PingvinOpenTag/LTAscetic/release_2(LCD,Joystck,TouchMemory,Reload,Antichiter,IrPowerControl,BattaryControl)/hardware/pcb/FreePCB/lib_extra/sm_ipc782.pdf

c:\freepcb_1000\lib_extra\sm_ipc782.pdf | page 1

## I2012CHIP

Author: Ivex
Source: SURFACE MOUNT DESIGN AND LAND PATTERN STANDARD SUBSECTION 8.3 (PAGE 3 OF 4)
Size: 3.6 x 1.6 mm
PIN(s) | PAD
TYPE | SHAPE | SIZE | HOLE
1-2 | SMT | Square | 1 mm | ---

Scale 2:1

## I3216CHIP

Author: Ivex
Source: SURFACE MOUNT DESIGN AND LAND PATTERN STANDARD SUBSECTION 8.3 (PAGE 3 OF 4)
Size: 4.9 x 2.2 mm
PIN(s) | PAD
TYPE | SHAPE | SIZE | HOLE
1-2 | SMT | Rect | 1.3 x 1.6 mm | ---

Scale 2:1

## I4516CHIP

Author: Ivex
Source: SURFACE MOUNT DESIGN AND LAND PATTERN STANDARD SUBSECTION 8.3 (PAGE 3 OF 4)
Size: 6.4 x 1.6 mm
PIN(s) | PAD
TYPE | SHAPE | SIZE | HOLE
1-2 | SMT | Rect | 1.6 x 1 mm | ---

Scale 2:1

## I2825PREC

Author: Ivex
Source: SURFACE MOUNT DESIGN AND LAND PATTERN STANDARD SUBSECTION 8.3 (PAGE 3 OF 4)
Size: 4.4 x 3 mm
PIN(s) | PAD
TYPE | SHAPE | SIZE | HOLE
1-2 | SMT | Rect | 1.4 x 2.4 mm | ---

Scale 2:1

## I3225PREC

Author: Ivex
Source: SURFACE MOUNT DESIGN AND LAND PATTERN STANDARD SUBSECTION 8.3 (PAGE 3 OF 4)
Size: 5.2 x 2.6 mm
PIN(s) | PAD
TYPE | SHAPE | SIZE | HOLE
1-2 | SMT | Rect | 1.8 x 2 mm | ---

## I4532PREC

Author: Ivex
Source: SURFACE MOUNT DESIGN AND LAND PATTERN STANDARD SUBSECTION 8.3 (PAGE 3 OF 4)
Size: 6.4 x 4.2 mm
PIN(s) | PAD
TYPE | SHAPE | SIZE | HOLE
1-2 | SMT | Rect | 1.8 x 3.6 mm | ---

Scale 2:1

## I5038PREC

Author: Ivex
Source: SURFACE MOUNT DESIGN AND LAND PATTERN STANDARD SUBSECTION 8.3 (PAGE 3 OF 4)
Size: 6.4 x 3.4 mm
PIN(s) | PAD
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
PIN(s) | PAD
TYPE | SHAPE | SIZE | HOLE
1-36 | SMT | Rect | 0.65 x 2.2 mm | ---

Scale 1:1

## CFP-MO-023/50

Author: Ivex
Source: - IPC-SM-782, REVISION A - AUGUST 1993 Size: 32.76 x 28.2 mm
PIN(s) | PAD
TYPE | SHAPE | SIZE | HOLE
1-50 | SMT | Rect | 0.65 x 2.2 mm | ---

Scale 1:1
