PingvinOpenTag/LTAscetic/release_1/hardware/pcb/layout.pdf

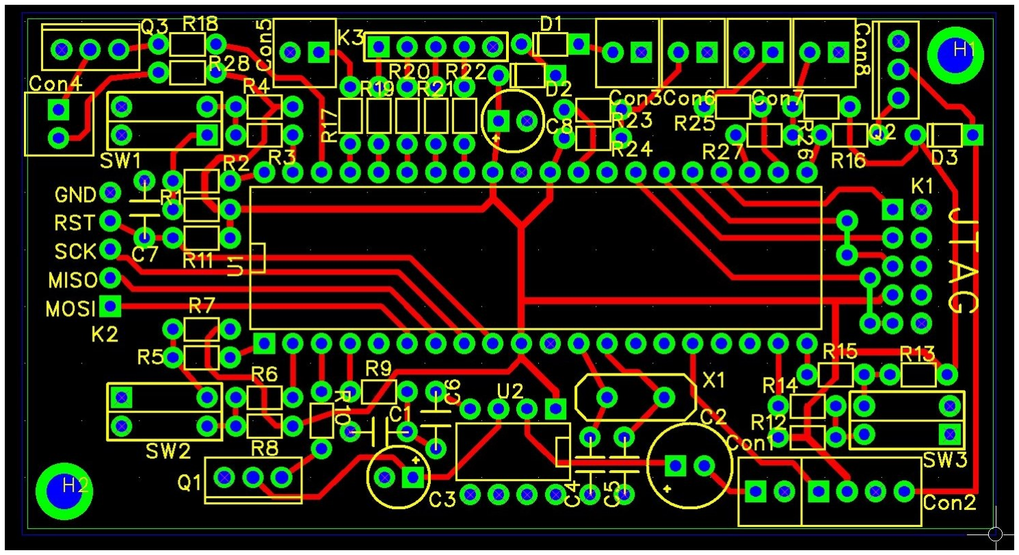
[picture p4: figure]
