PingvinOpenTag/LTAscetic/5_provodov.jpg

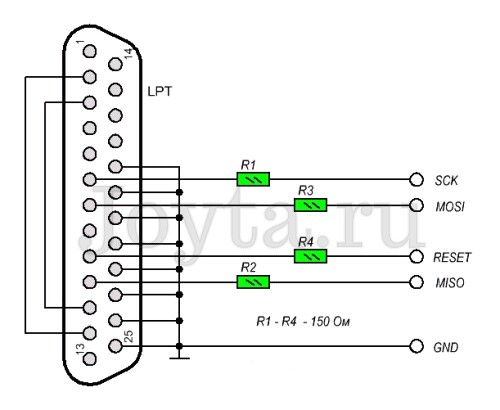
5_provodov.jpg
