PingvinOpenTag/LTAscetic/programmer.gif

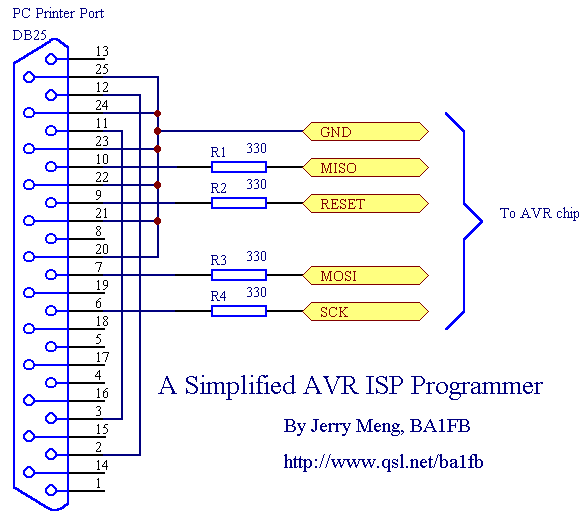
programmer.gif
