PingvinOpenTag/LTAscetic/release_2(LCD,Joystck,TouchMemory,Reload,Antichiter,IrPowerControl,BattaryControl)/hardware/scheme/lcd_shield_smd_scheme.jpeg

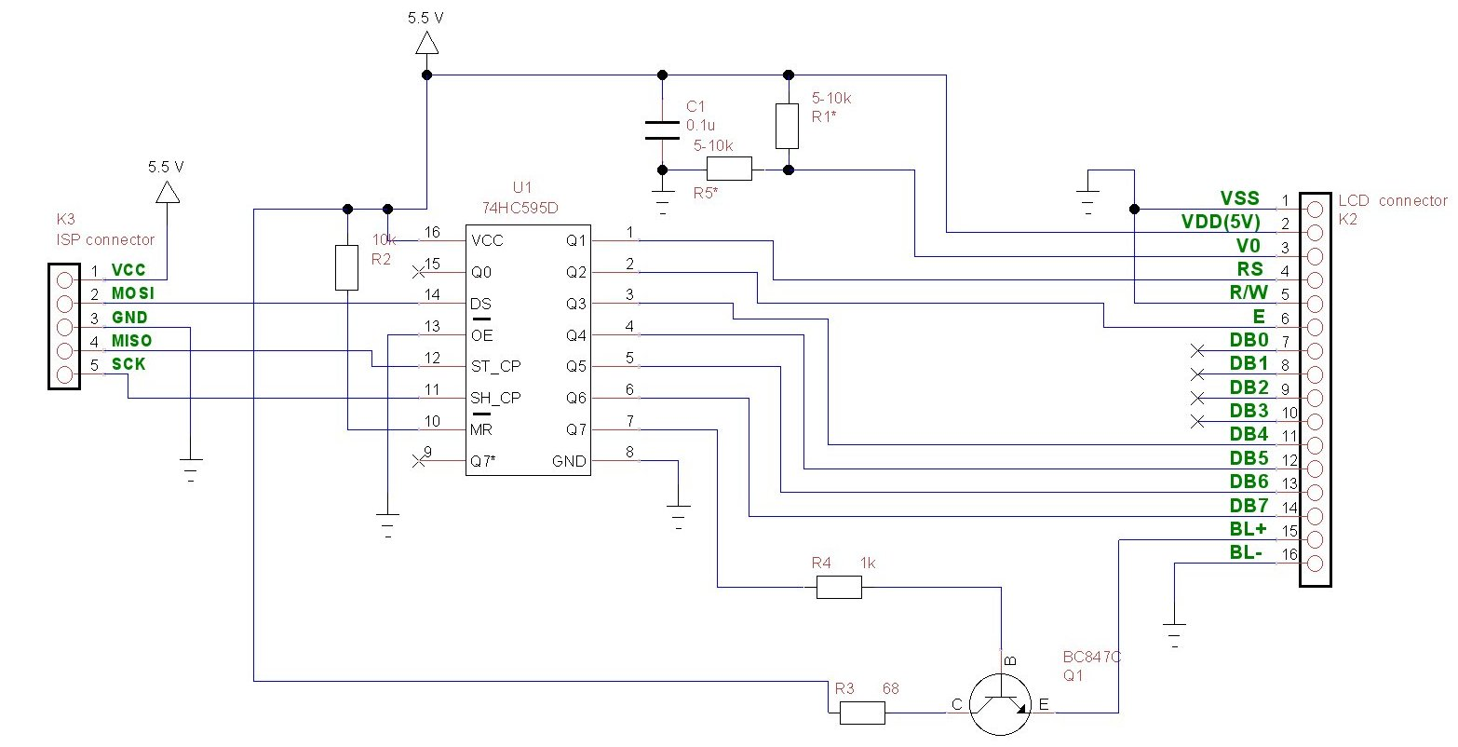
release_2(LCD,Joystck,TouchMemory,Reload,Antichiter,IrPowerControl,BattaryControl)/hardware/scheme/lcd_shield_smd_scheme.jpeg
