PingvinOpenTag/LTAscetic/release_3(all_thet_is_in_the_release_2,extern_EEPROM_RS232_BOOTLOADER)/firmware/LTAscetic_Atmega32/Ascet_3_0_with_bootloader_fuses_AVRStudio4.png

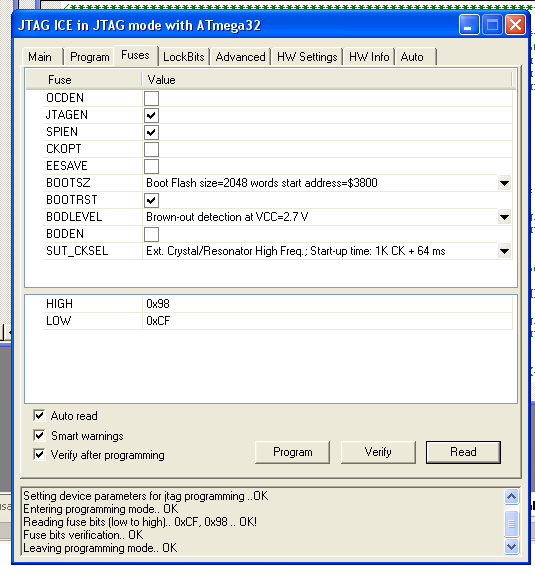
release_3(all_thet_is_in_the_release_2,extern_EEPROM_RS232_BOOTLOADER)/firmware/LTAscetic_Atmega32/Ascet_3_0_with_bootloader_fuses_AVRStudio4.png
