PingvinOpenTag/LTAscetic/release_3(all_thet_is_in_the_release_2,extern_EEPROM_RS232_BOOTLOADER)/hardware/scheme/Ascetic_3_LCD_shield_scheme.jpeg

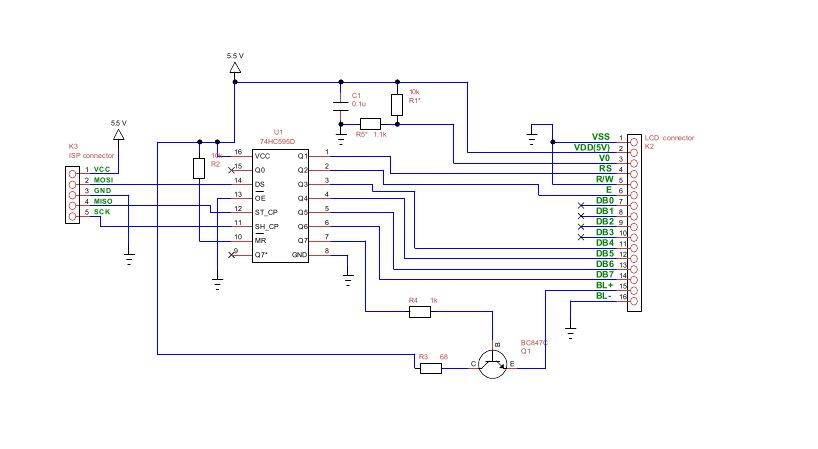
release_3(all_thet_is_in_the_release_2,extern_EEPROM_RS232_BOOTLOADER)/hardware/scheme/Ascetic_3_LCD_shield_scheme.jpeg
