PingvinOpenTag/LTAscetic/release_3_1(SMD,fix_flesh_led_bag,firmware_up_to_56000Hz_IR_F0)/hardware/scheme/Ascet_3_1_IR_Sensor_scheme.jpeg

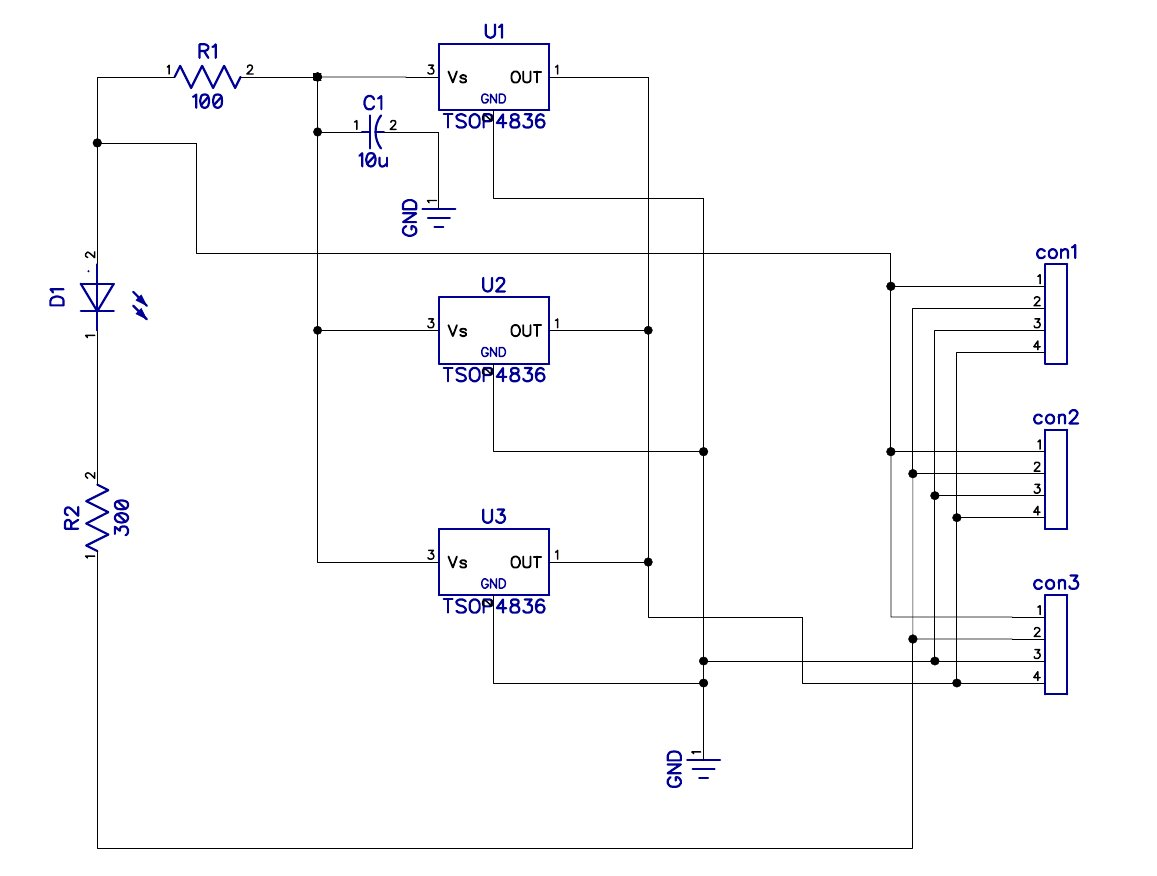
release_3_1(SMD,fix_flesh_led_bag,firmware_up_to_56000Hz_IR_F0)/hardware/scheme/Ascet_3_1_IR_Sensor_scheme.jpeg
