PingvinOpenTag/LTAscetic/release_3_1(SMD,fix_flesh_led_bag,firmware_up_to_56000Hz_IR_F0)/firmware/LTAscet_3_1_Atmega32/Ascet_3_1_without_bootloader_PonyProg_fuses.jpeg

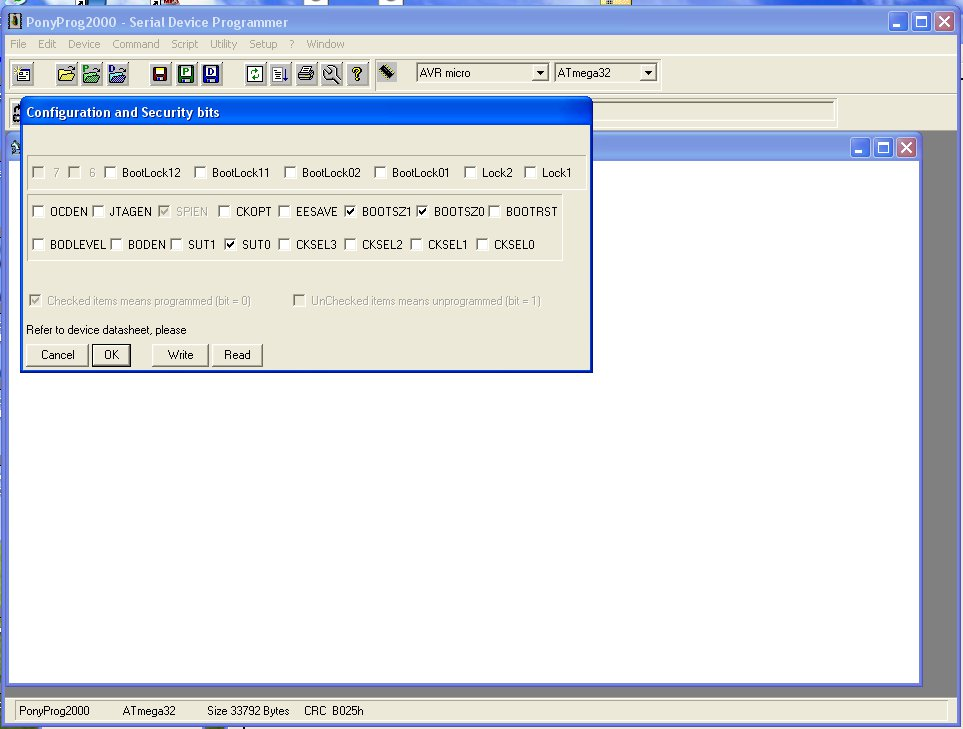
release_3_1(SMD,fix_flesh_led_bag,firmware_up_to_56000Hz_IR_F0)/firmware/LTAscet_3_1_Atmega32/Ascet_3_1_without_bootloader_PonyProg_fuses.jpeg
