PingvinOpenTag/LTAscetic/release_2(LCD,Joystck,TouchMemory,Reload,Antichiter,IrPowerControl,BattaryControl)/hardware/pcb/FreePCB/lib_extra/elfa_cap.pdf

1206

0805

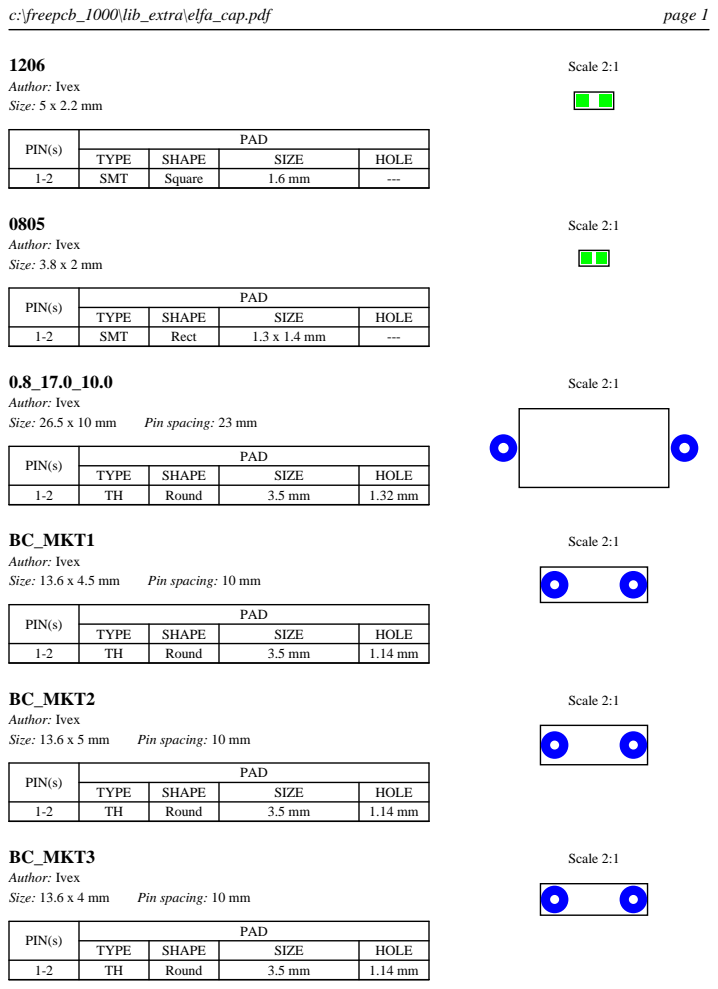
[picture p30: page 1]
c:\freepcb_1000\lib_extra\elfa_cap.pdf; page 1; Author: Ivex Size: 5 x 2.2 mm; Scale 2:1; Author: Ivex Size: 3.8 x 2 mm; Author: Ivex; Size: 26.5 x 10 mm; Pin spacing: 23 mm; BC_MKT1; Size: 13.6 x 4.5 mm; Pin spacing: 10 mm; BC_MKT2; Size: 13.6 x 5 mm; BC_MKT3; Size: 13.6 x 4 mm

PIN(s) | PAD

TYPE | SHAPE | SIZE | HOLE

1-2 | SMT | Square | 1.6 mm | ---

1-2 | SMT | Rect | 1.3 x 1.4 mm | ---

1-2 | TH | Round | 3.5 mm | 1.32 mm

1-2 | TH | Round | 3.5 mm | 1.14 mm

## BC_MKT4

## BC_MKT5

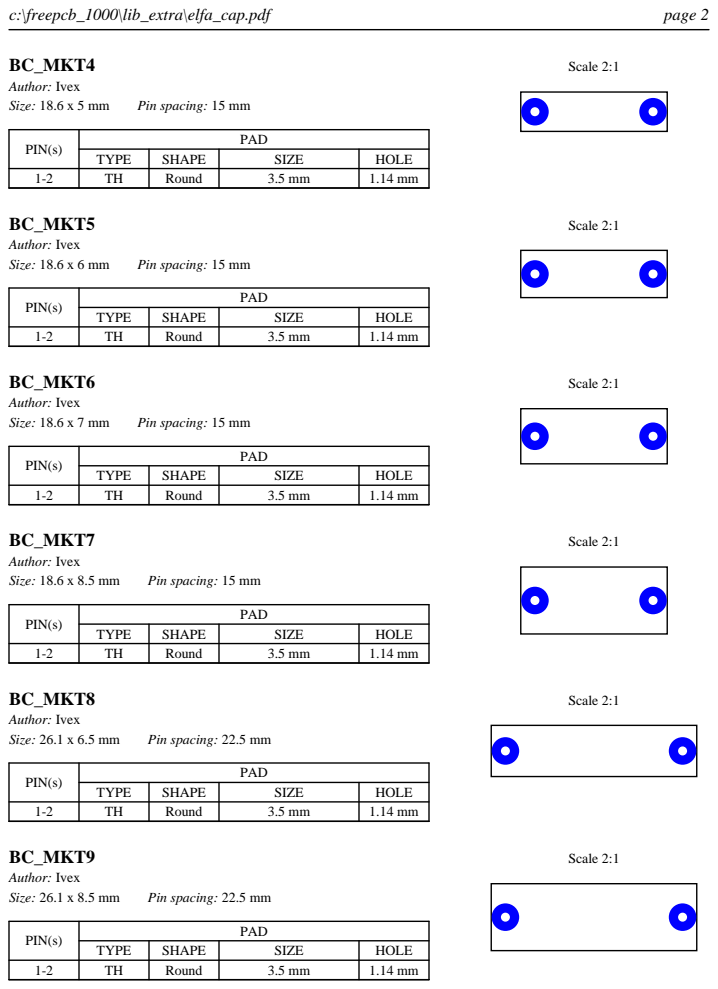
[picture p31: page 2]
Author: Ivex; Size: 18.6 x 5 mm; Pin spacing: 15 mm; Size: 18.6 x 6 mm; Scale 2:1; BC_MKT6; Size: 18.6 x 7 mm; BC_MKT7; Size: 18.6 x 8.5 mm; BC_MKT8; Size: 26.1 x 6.5 mm; Pin spacing: 22.5 mm; BC_MKT9; Size: 26.1 x 8.5 mm

PIN(s) | PAD

TYPE | SHAPE | SIZE | HOLE

1-2 | TH | Round | 3.5 mm | 1.14 mm

## BC_MKT10

## BC_MKT11

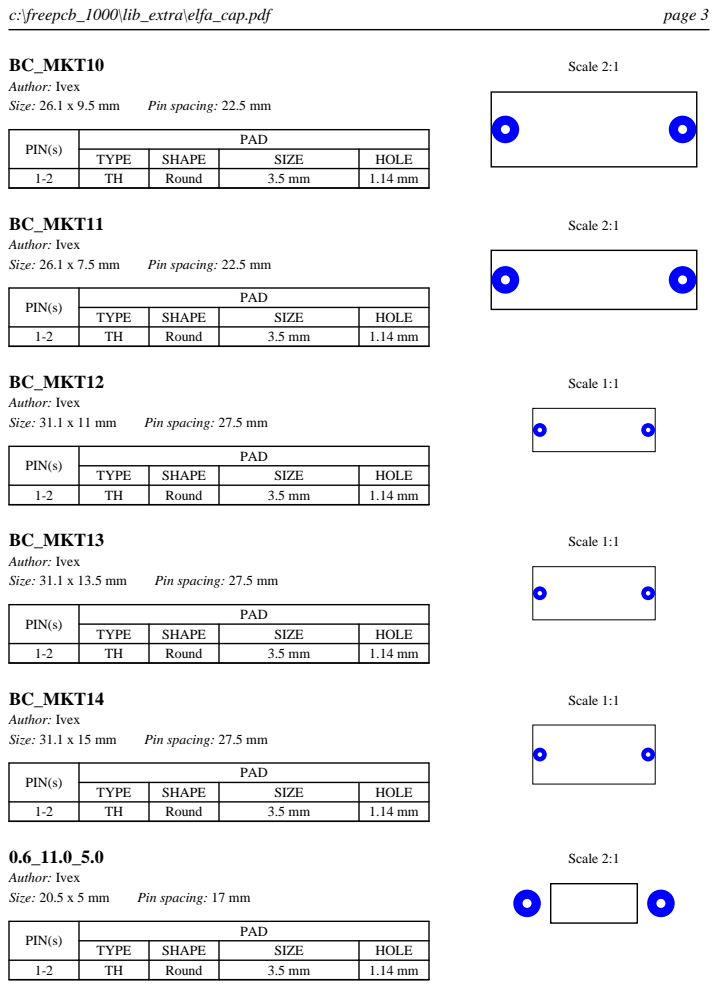
[picture p32: page 3]
Author: Ivex; Size: 26.1 x 9.5 mm; Pin spacing: 22.5 mm; Size: 26.1 x 7.5 mm; Scale 2:1; BC_MKT12; Size: 31.1 x 11 mm; Pin spacing: 27.5 mm; Scale 1:1; BC_MKT13; Size: 31.1 x 13.5 mm; BC_MKT14; Size: 31.1 x 15 mm; Size: 20.5 x 5 mm; Pin spacing: 17 mm

PIN(s) | PAD

TYPE | SHAPE | SIZE | HOLE

1-2 | TH | Round | 3.5 mm | 1.14 mm

0.6_15.0_5.5

0.6_15.0_6.0

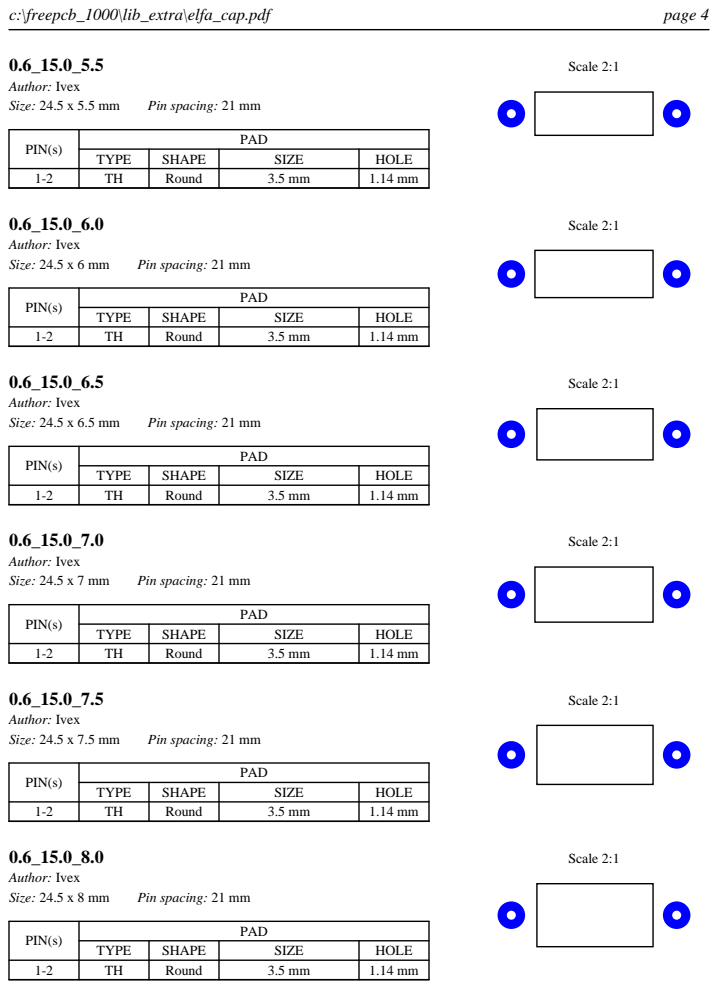
[picture p33: page 4]
Author: Ivex; Size: 24.5 x 5.5 mm; Pin spacing: 21 mm; Size: 24.5 x 6 mm; Scale 2:1; Size: 24.5 x 6.5 mm; Size: 24.5 x 7 mm; Size: 24.5 x 7.5 mm; Size: 24.5 x 8 mm

PIN(s) | PAD

TYPE | SHAPE | SIZE | HOLE

1-2 | TH | Round | 3.5 mm | 1.14 mm

## BC_LS2.54

## BC_LS5.08

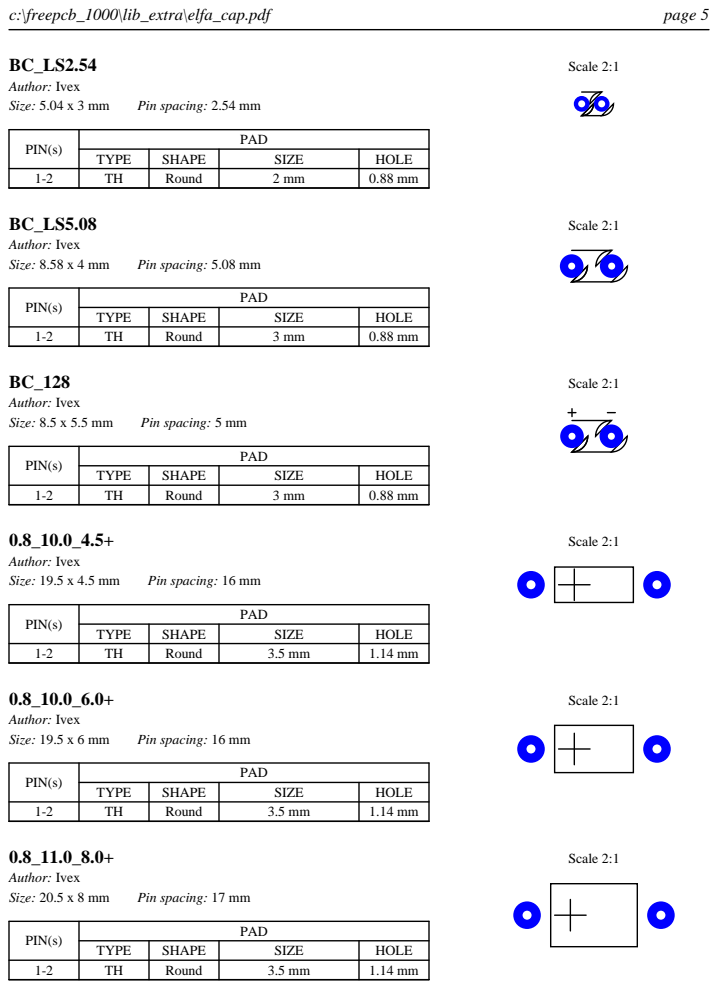
[picture p34: page 5]
Author: Ivex; Size: 5.04 x 3 mm; Pin spacing: 2.54 mm; Size: 8.58 x 4 mm; Pin spacing: 5.08 mm; Scale 2:1; Size: 8.5 x 5.5 mm; Pin spacing: 5 mm; Size: 19.5 x 4.5 mm; Pin spacing: 16 mm; Size: 19.5 x 6 mm; Size: 20.5 x 8 mm; Pin spacing: 17 mm

PIN(s) | PAD

TYPE | SHAPE | SIZE | HOLE

1-2 | TH | Round | 2 mm | 0.88 mm

1-2 | TH | Round | 3 mm | 0.88 mm

1-2 | TH | Round | 3.5 mm | 1.14 mm

0.8_18.0_10.0+

0.8_18.0_8.0+

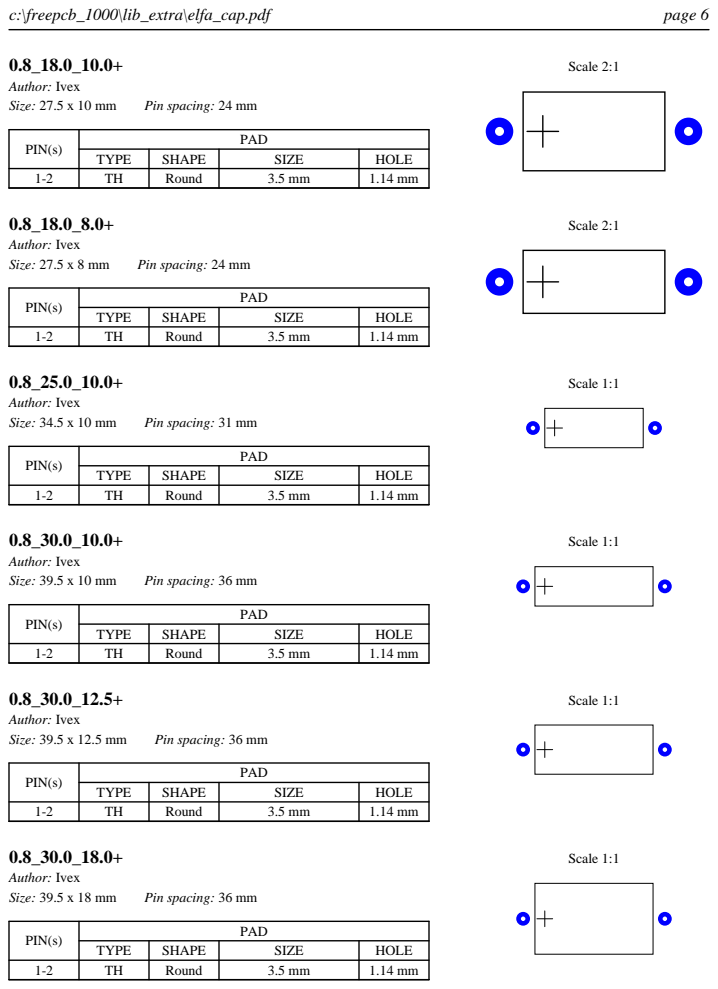
[picture p35: page 6]
Author: Ivex; Size: 27.5 x 10 mm; Pin spacing: 24 mm; Size: 27.5 x 8 mm; Scale 2:1; Size: 34.5 x 10 mm; Pin spacing: 31 mm; Scale 1:1; Size: 39.5 x 10 mm; Pin spacing: 36 mm; Size: 39.5 x 12.5 mm; Size: 39.5 x 18 mm

PIN(s) | PAD

TYPE | SHAPE | SIZE | HOLE

1-2 | TH | Round | 3.5 mm | 1.14 mm

0.8_40.0_21.0+

0.8_36.0_14.0+

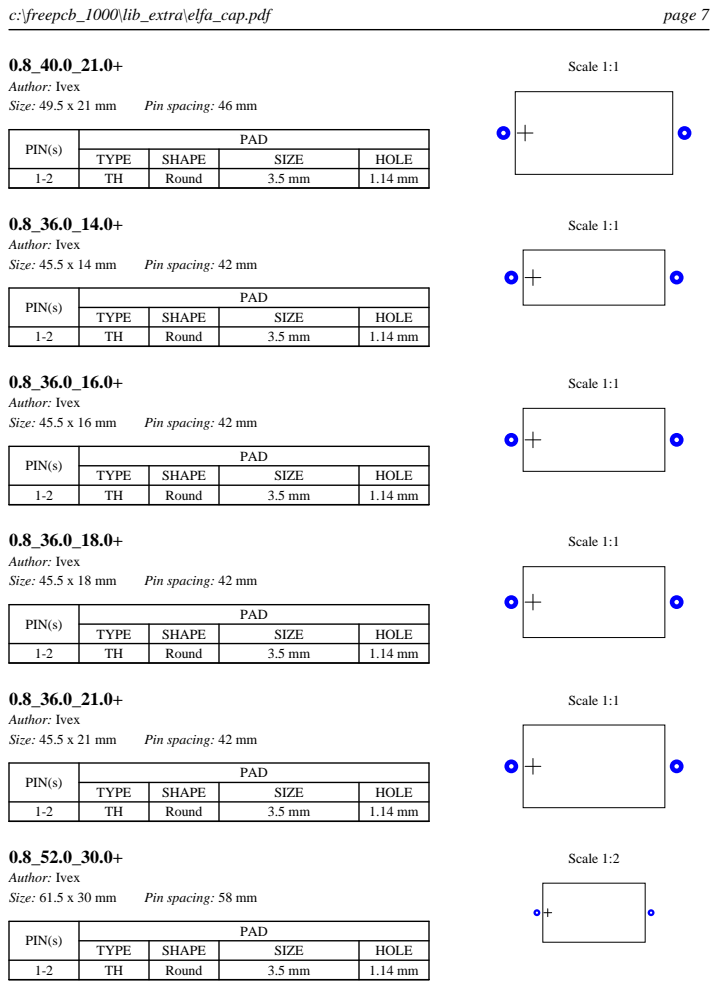
[picture p36: page 7]
Author: Ivex; Size: 49.5 x 21 mm; Pin spacing: 46 mm; Scale 1:1; Size: 45.5 x 14 mm; Pin spacing: 42 mm; Size: 45.5 x 16 mm; Size: 45.5 x 18 mm; Size: 45.5 x 21 mm; Size: 61.5 x 30 mm; Pin spacing: 58 mm; Scale 1:2

PIN(s) | PAD

TYPE | SHAPE | SIZE | HOLE

1-2 | TH | Round | 3.5 mm | 1.14 mm

0.8_49.0_25.0+

0.8_18.0_6.5+

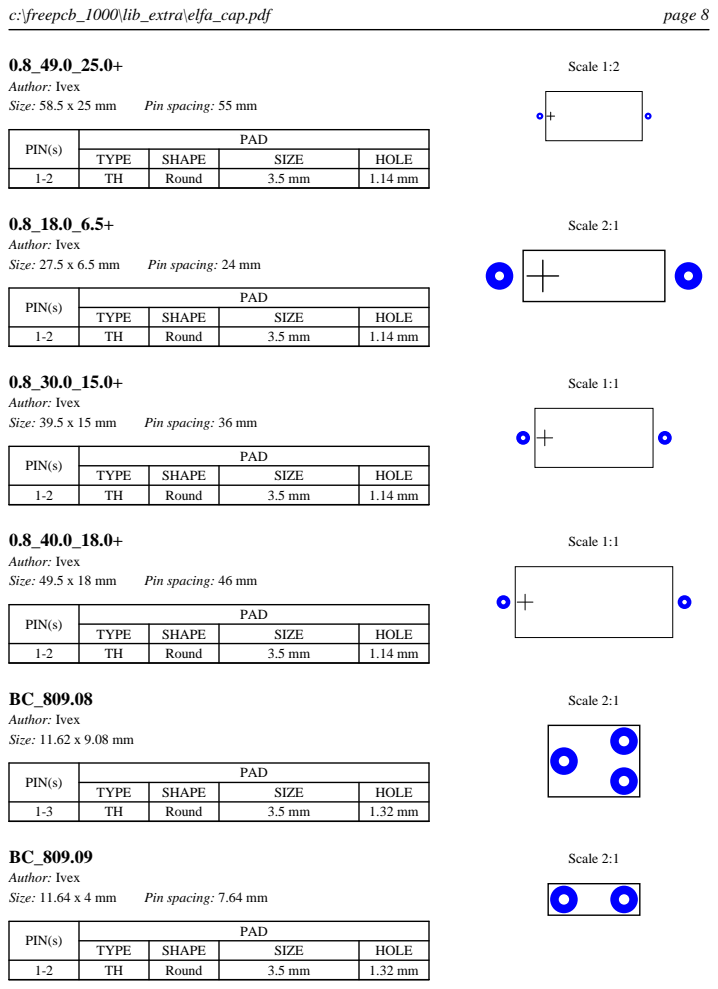
[picture p37: page 8]
Author: Ivex; Size: 58.5 x 25 mm; Pin spacing: 55 mm; Scale 1:2; Size: 27.5 x 6.5 mm; Pin spacing: 24 mm; Scale 2:1; Size: 39.5 x 15 mm; Pin spacing: 36 mm; Scale 1:1; Size: 49.5 x 18 mm; Pin spacing: 46 mm; Author: Ivex Size: 11.62 x 9.08 mm; Size: 11.64 x 4 mm; Pin spacing: 7.64 mm

PIN(s) | PAD

TYPE | SHAPE | SIZE | HOLE

1-2 | TH | Round | 3.5 mm | 1.14 mm

1-3 | TH | Round | 3.5 mm | 1.32 mm

1-2 | TH | Round | 3.5 mm | 1.32 mm

## BC_808.11

## ELNA_RJH8

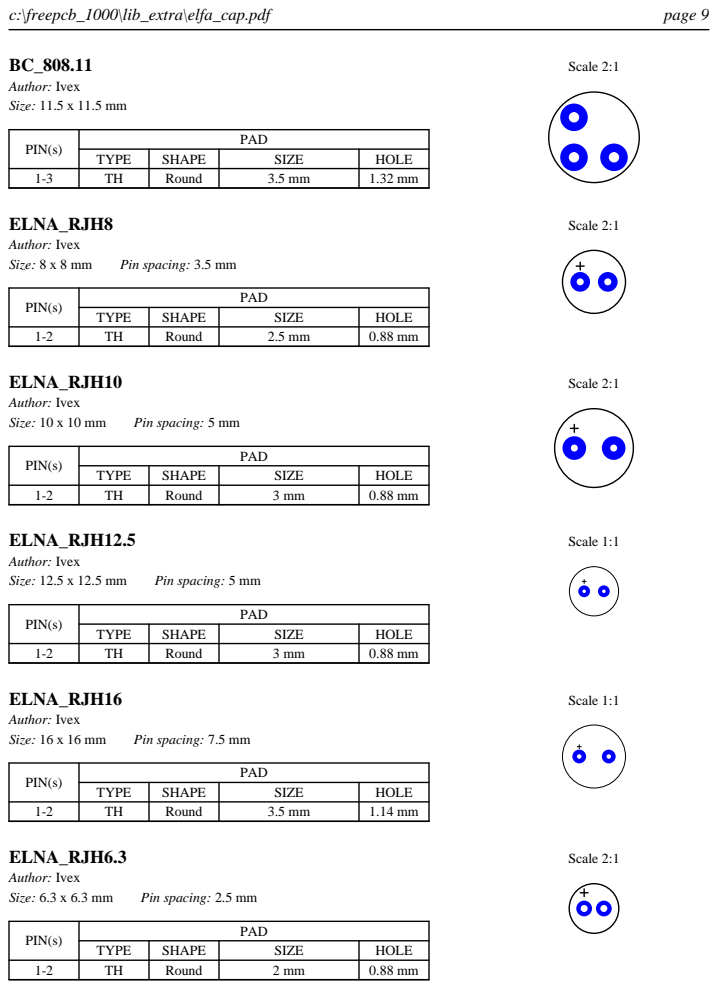
[picture p38: page 9]
Author: Ivex Size: 11.5 x 11.5 mm; Author: Ivex; Size: 8 x 8 mm; Pin spacing: 3.5 mm; Scale 2:1; ELNA_RJH10; Size: 10 x 10 mm; Pin spacing: 5 mm; ELNA_RJH12.5; Size: 12.5 x 12.5 mm; Scale 1:1; ELNA_RJH16; Size: 16 x 16 mm; Pin spacing: 7.5 mm; ELNA_RJH6.3; Size: 6.3 x 6.3 mm; Pin spacing: 2.5 mm

PIN(s) | PAD

TYPE | SHAPE | SIZE | HOLE

1-3 | TH | Round | 3.5 mm | 1.32 mm

1-2 | TH | Round | 2.5 mm | 0.88 mm

1-2 | TH | Round | 3 mm | 0.88 mm

1-2 | TH | Round | 3.5 mm | 1.14 mm

1-2 | TH | Round | 2 mm | 0.88 mm

## ELNA_RJH5

## ELNA_RJH18

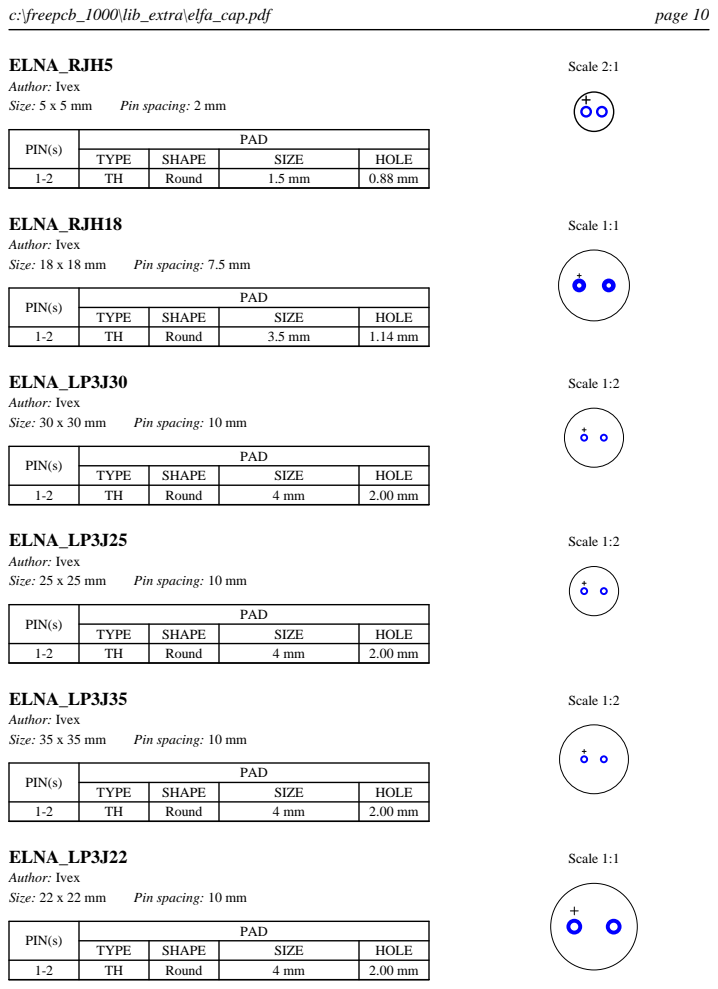
[picture p39: page 10]
Author: Ivex; Size: 5 x 5 mm; Pin spacing: 2 mm; Size: 18 x 18 mm; Pin spacing: 7.5 mm; Scale 1:1; ELNA_LP3J30; Size: 30 x 30 mm; Pin spacing: 10 mm; Scale 1:2; ELNA_LP3J25; Size: 25 x 25 mm; ELNA_LP3J35; Size: 35 x 35 mm; ELNA_LP3J22; Size: 22 x 22 mm

PIN(s) | PAD

TYPE | SHAPE | SIZE | HOLE

1-2 | TH | Round | 1.5 mm | 0.88 mm

1-2 | TH | Round | 3.5 mm | 1.14 mm

1-2 | TH | Round | 4 mm | 2.00 mm

## ELNA_DB13.5

## ELNA_DB21.5

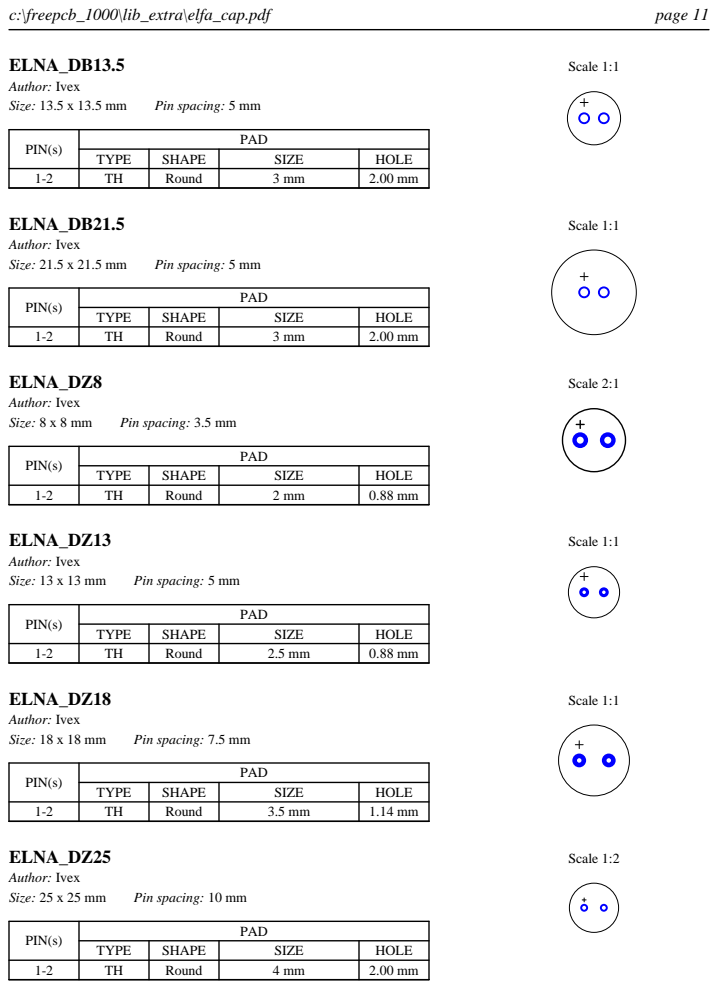
[picture p40: page 11]
Author: Ivex; Size: 13.5 x 13.5 mm; Pin spacing: 5 mm; Scale 1:1; Size: 21.5 x 21.5 mm; ELNA_DZ8; Size: 8 x 8 mm; Pin spacing: 3.5 mm; Scale 2:1; ELNA_DZ13; Size: 13 x 13 mm; ELNA_DZ18; Size: 18 x 18 mm; Pin spacing: 7.5 mm; ELNA_DZ25; Size: 25 x 25 mm; Pin spacing: 10 mm; Scale 1:2

PIN(s) | PAD

TYPE | SHAPE | SIZE | HOLE

1-2 | TH | Round | 3 mm | 2.00 mm

1-2 | TH | Round | 2 mm | 0.88 mm

1-2 | TH | Round | 2.5 mm | 0.88 mm

1-2 | TH | Round | 3.5 mm | 1.14 mm

1-2 | TH | Round | 4 mm | 2.00 mm

## JAM_4

## JAM_5

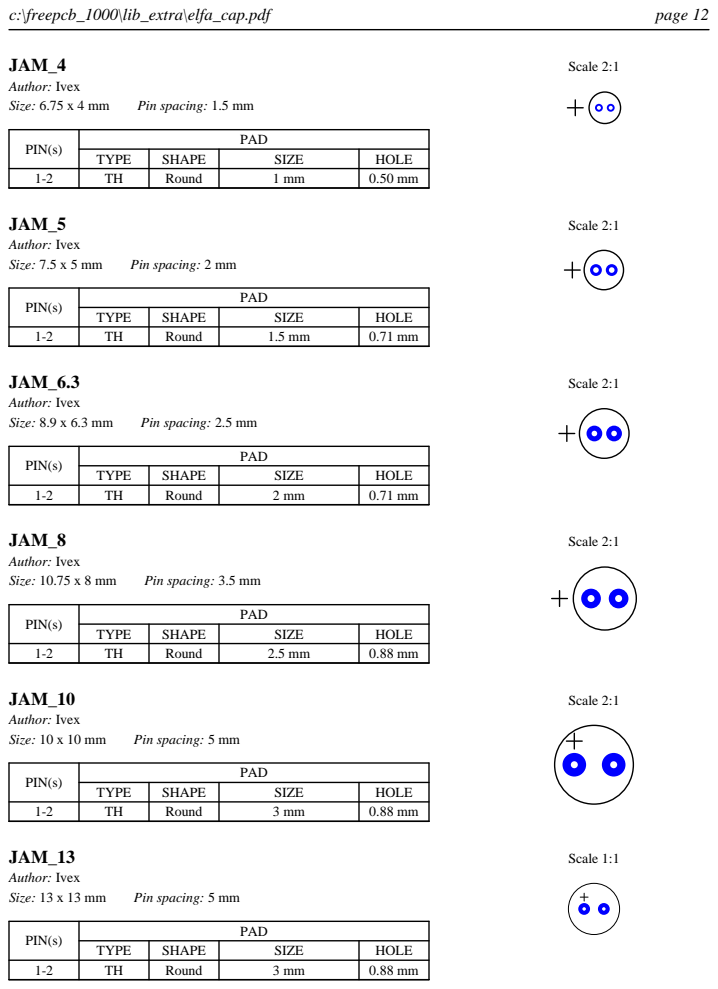
[picture p41: page 12]
Author: Ivex; Size: 6.75 x 4 mm; Pin spacing: 1.5 mm; Size: 7.5 x 5 mm; Pin spacing: 2 mm; Scale 2:1; JAM_6.3; Size: 8.9 x 6.3 mm; Pin spacing: 2.5 mm; JAM_8; Size: 10.75 x 8 mm; Pin spacing: 3.5 mm; JAM_10; Size: 10 x 10 mm; Pin spacing: 5 mm; JAM_13; Size: 13 x 13 mm; Scale 1:1

PIN(s) | PAD

TYPE | SHAPE | SIZE | HOLE

1-2 | TH | Round | 1 mm | 0.50 mm

1-2 | TH | Round | 1.5 mm | 0.71 mm

1-2 | TH | Round | 2 mm | 0.71 mm

1-2 | TH | Round | 2.5 mm | 0.88 mm

1-2 | TH | Round | 3 mm | 0.88 mm

## JAM_16

## JAM_18

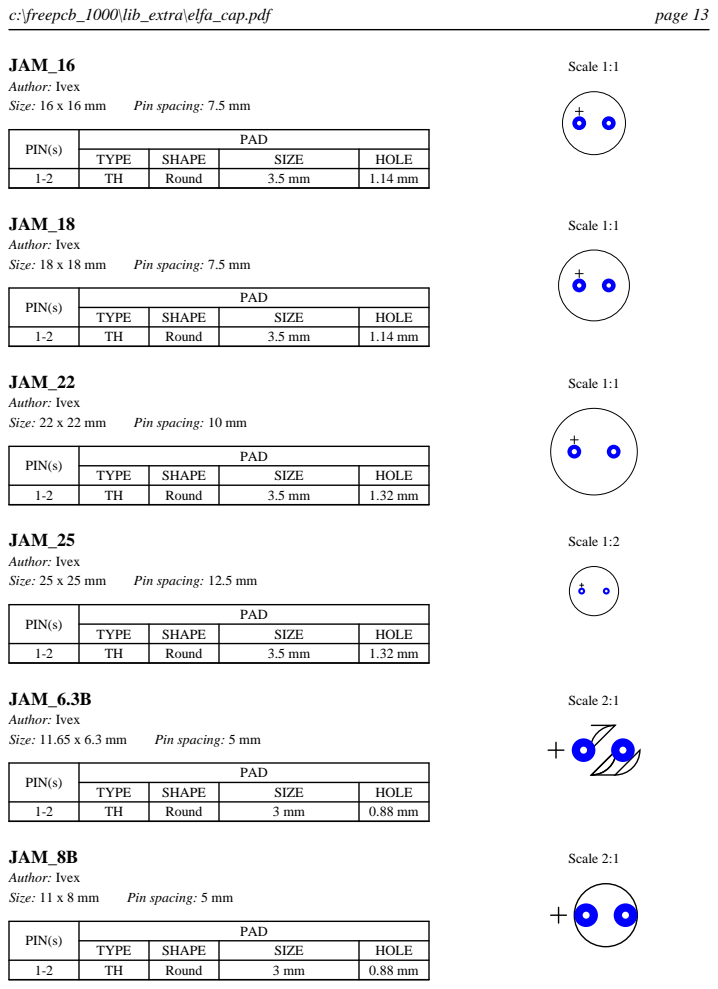
[picture p42: page 13]
Author: Ivex; Size: 16 x 16 mm; Pin spacing: 7.5 mm; Scale 1:1; Size: 18 x 18 mm; JAM_22; Size: 22 x 22 mm; Pin spacing: 10 mm; JAM_25; Size: 25 x 25 mm; Pin spacing: 12.5 mm; Scale 1:2; JAM_6.3B; Size: 11.65 x 6.3 mm; Pin spacing: 5 mm; Scale 2:1; JAM_8B; Size: 11 x 8 mm

PIN(s) | PAD

TYPE | SHAPE | SIZE | HOLE

1-2 | TH | Round | 3.5 mm | 1.14 mm

1-2 | TH | Round | 3.5 mm | 1.32 mm

1-2 | TH | Round | 3 mm | 0.88 mm

## JAM_5B

## KEM_C315/C320

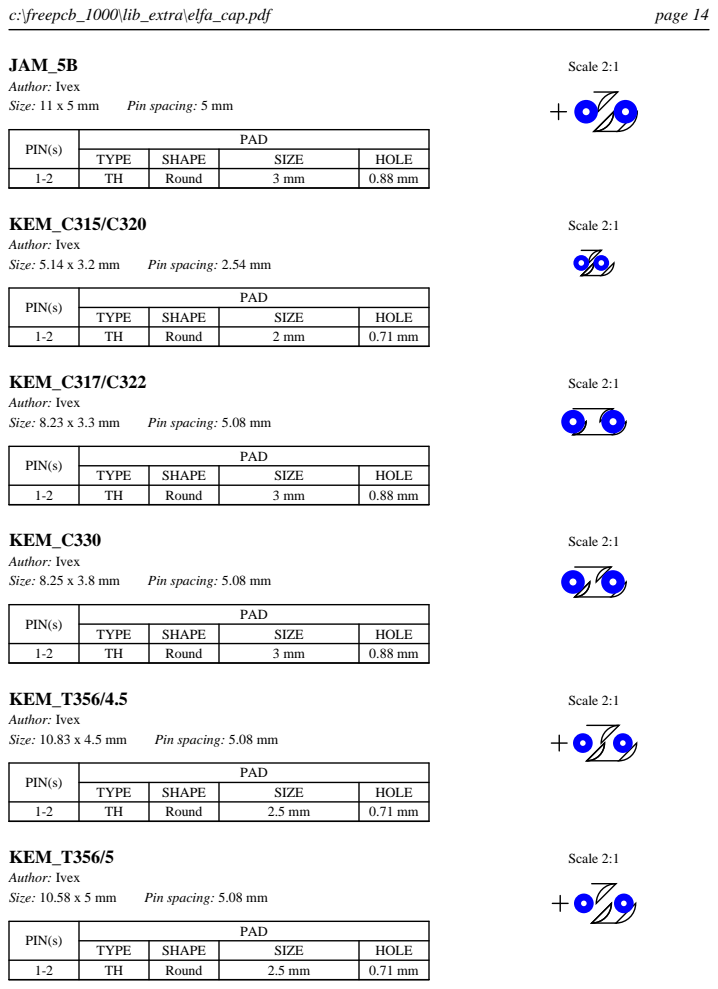
[picture p43: page 14]
Author: Ivex; Size: 11 x 5 mm; Pin spacing: 5 mm; Size: 5.14 x 3.2 mm; Pin spacing: 2.54 mm; Scale 2:1; KEM_C317/C322; Size: 8.23 x 3.3 mm; Pin spacing: 5.08 mm; KEM_C330; Size: 8.25 x 3.8 mm; KEM_T356/4.5; Size: 10.83 x 4.5 mm; KEM_T356/5; Size: 10.58 x 5 mm

PIN(s) | PAD

TYPE | SHAPE | SIZE | HOLE

1-2 | TH | Round | 3 mm | 0.88 mm

1-2 | TH | Round | 2 mm | 0.71 mm

1-2 | TH | Round | 2.5 mm | 0.71 mm

## KEM_T356/5.5

## KEM_T356/6

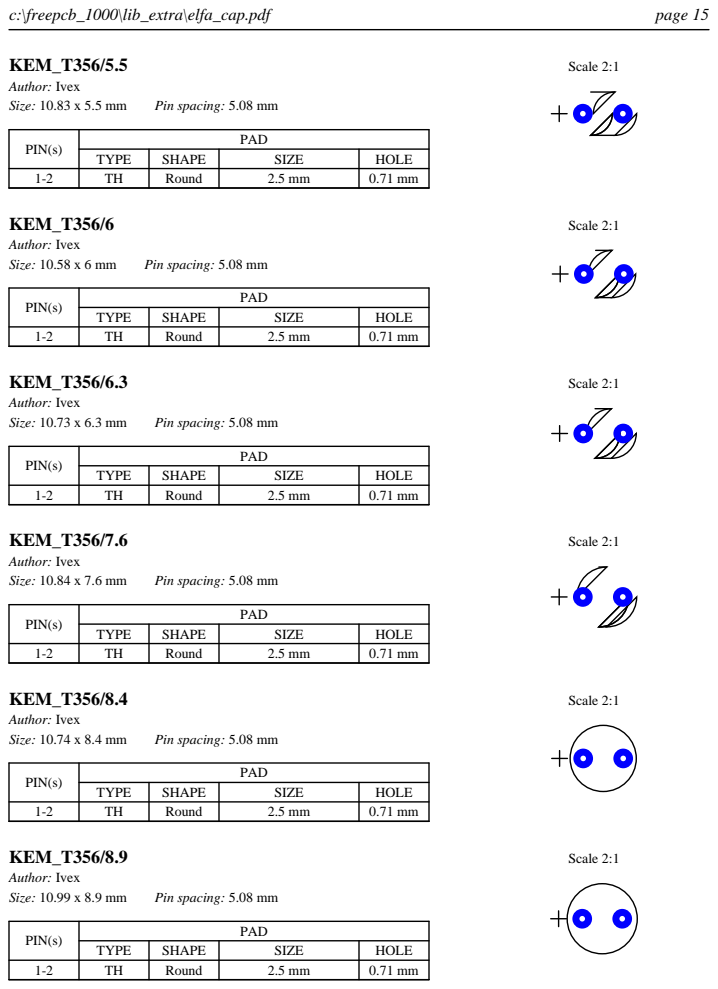
[picture p44: page 15]
Author: Ivex; Size: 10.83 x 5.5 mm; Pin spacing: 5.08 mm; Size: 10.58 x 6 mm; Scale 2:1; KEM_T356/6.3; Size: 10.73 x 6.3 mm; KEM_T356/7.6; Size: 10.84 x 7.6 mm; KEM_T356/8.4; Size: 10.74 x 8.4 mm; KEM_T356/8.9; Size: 10.99 x 8.9 mm

PIN(s) | PAD

TYPE | SHAPE | SIZE | HOLE

1-2 | TH | Round | 2.5 mm | 0.71 mm

## KEM_T350/4.5

## KEM_T350/5.0

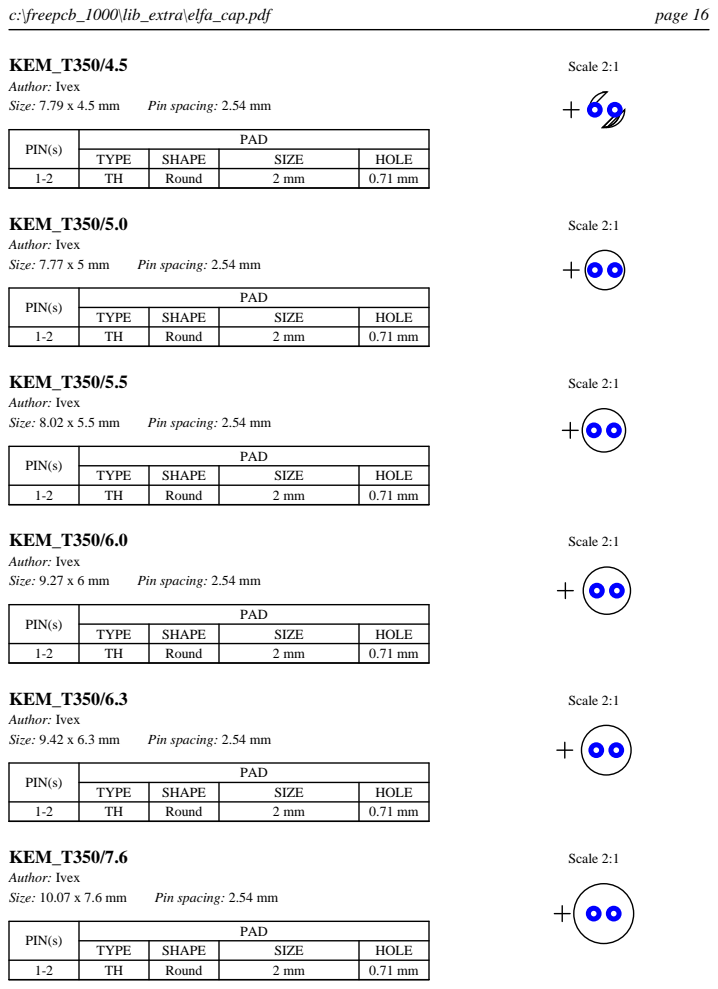
[picture p45: page 16]
Author: Ivex; Size: 7.79 x 4.5 mm; Pin spacing: 2.54 mm; Size: 7.77 x 5 mm; Scale 2:1; KEM_T350/5.5; Size: 8.02 x 5.5 mm; KEM_T350/6.0; Size: 9.27 x 6 mm; KEM_T350/6.3; Size: 9.42 x 6.3 mm; KEM_T350/7.6; Size: 10.07 x 7.6 mm

PIN(s) | PAD

TYPE | SHAPE | SIZE | HOLE

1-2 | TH | Round | 2 mm | 0.71 mm

## KEM_AXL12.7

## KEM_AXL17.8

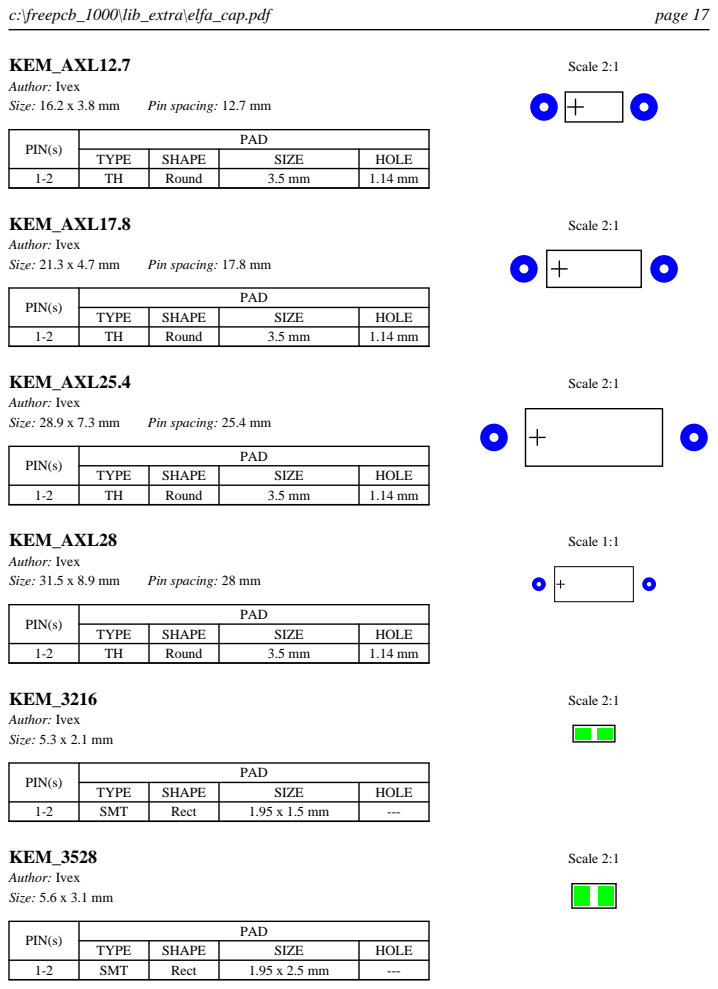
[picture p46: page 17]
Author: Ivex; Size: 16.2 x 3.8 mm; Pin spacing: 12.7 mm; Size: 21.3 x 4.7 mm; Pin spacing: 17.8 mm; Scale 2:1; KEM_AXL25.4; Size: 28.9 x 7.3 mm; Pin spacing: 25.4 mm; KEM_AXL28; Size: 31.5 x 8.9 mm; Pin spacing: 28 mm; Scale 1:1; KEM_3216; Author: Ivex Size: 5.3 x 2.1 mm; KEM_3528; Author: Ivex Size: 5.6 x 3.1 mm

PIN(s) | PAD

TYPE | SHAPE | SIZE | HOLE

1-2 | TH | Round | 3.5 mm | 1.14 mm

1-2 | SMT | Rect | 1.95 x 1.5 mm | ---

1-2 | SMT | Rect | 1.95 x 2.5 mm | ---

## KEM_6032

## KEM_7343

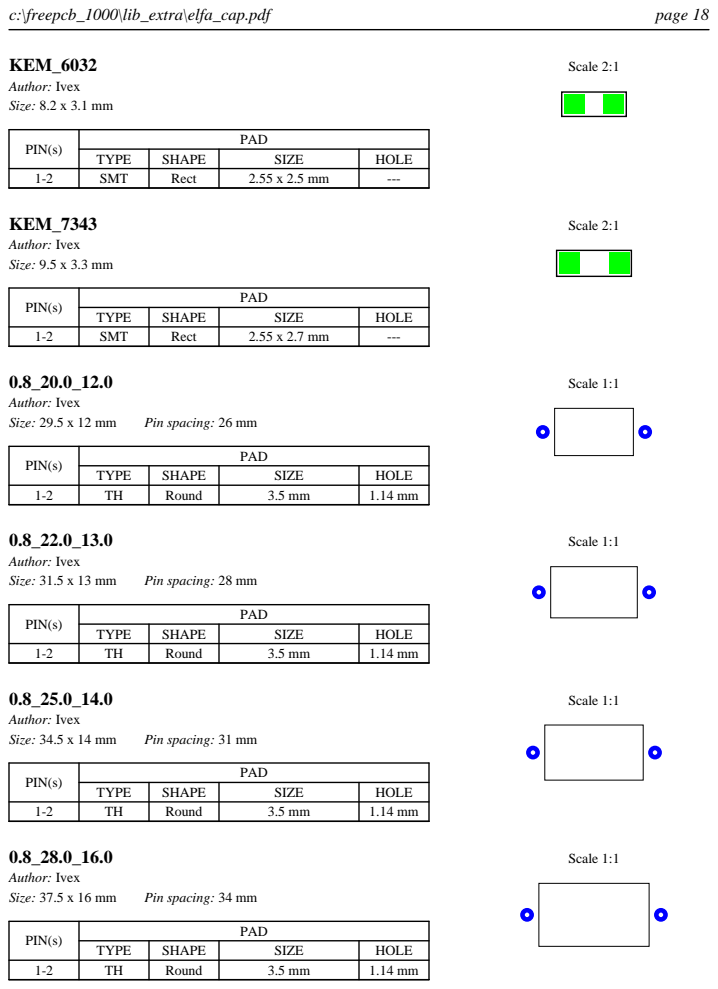
[picture p47: page 18]
Author: Ivex Size: 8.2 x 3.1 mm; Author: Ivex Size: 9.5 x 3.3 mm; Scale 2:1; Author: Ivex; Size: 29.5 x 12 mm; Pin spacing: 26 mm; Scale 1:1; Size: 31.5 x 13 mm; Pin spacing: 28 mm; Size: 34.5 x 14 mm; Pin spacing: 31 mm; Size: 37.5 x 16 mm; Pin spacing: 34 mm

PIN(s) | PAD

TYPE | SHAPE | SIZE | HOLE

1-2 | SMT | Rect | 2.55 x 2.5 mm | ---

1-2 | SMT | Rect | 2.55 x 2.7 mm | ---

1-2 | TH | Round | 3.5 mm | 1.14 mm

0.8_28.0_19.0

0.8_30.0_19.0

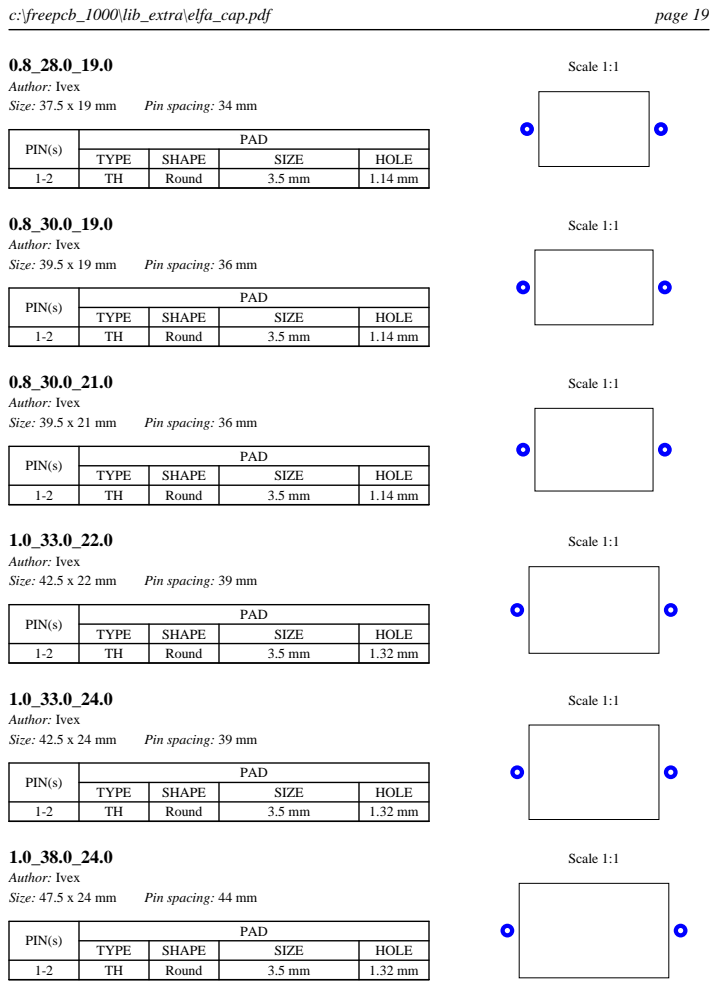
[picture p48: page 19]
Author: Ivex; Size: 37.5 x 19 mm; Pin spacing: 34 mm; Scale 1:1; Size: 39.5 x 19 mm; Pin spacing: 36 mm; Size: 39.5 x 21 mm; Size: 42.5 x 22 mm; Pin spacing: 39 mm; Size: 42.5 x 24 mm; Size: 47.5 x 24 mm; Pin spacing: 44 mm

PIN(s) | PAD

TYPE | SHAPE | SIZE | HOLE

1-2 | TH | Round | 3.5 mm | 1.14 mm

1-2 | TH | Round | 3.5 mm | 1.32 mm

1.0_38.0_26.0

1.0_43.0_26.0

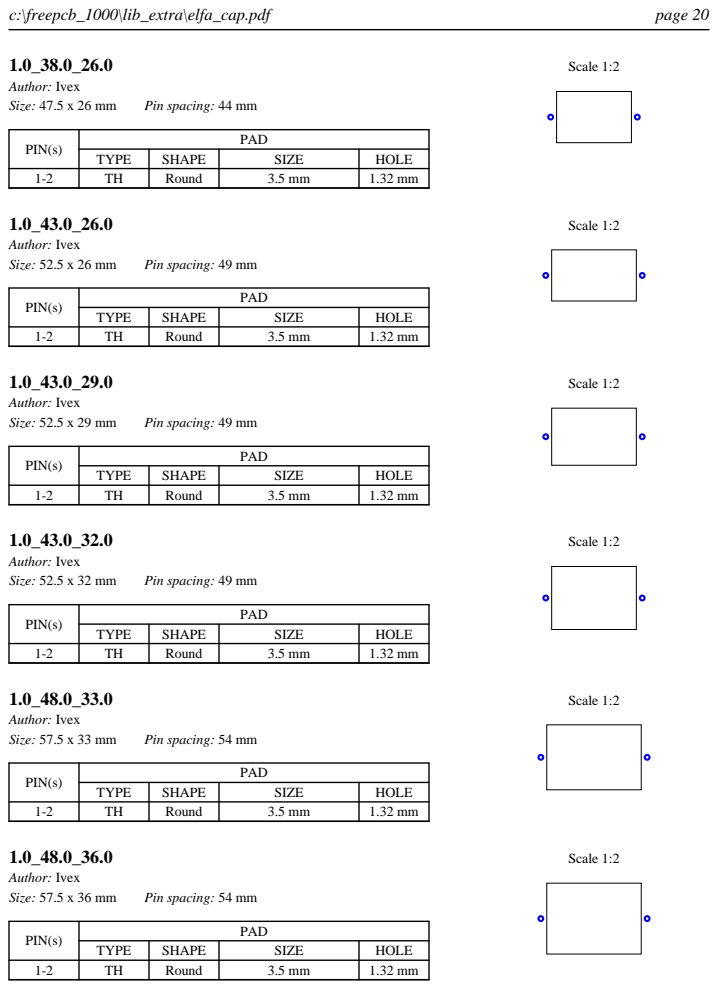
[picture p49: page 20]
Author: Ivex; Size: 47.5 x 26 mm; Pin spacing: 44 mm; Scale 1:2; Size: 52.5 x 26 mm; Pin spacing: 49 mm; Size: 52.5 x 29 mm; Size: 52.5 x 32 mm; Size: 57.5 x 33 mm; Pin spacing: 54 mm; Size: 57.5 x 36 mm

PIN(s) | PAD

TYPE | SHAPE | SIZE | HOLE

1-2 | TH | Round | 3.5 mm | 1.32 mm

1.2_53.0_37.0

1.2_53.0_40.0

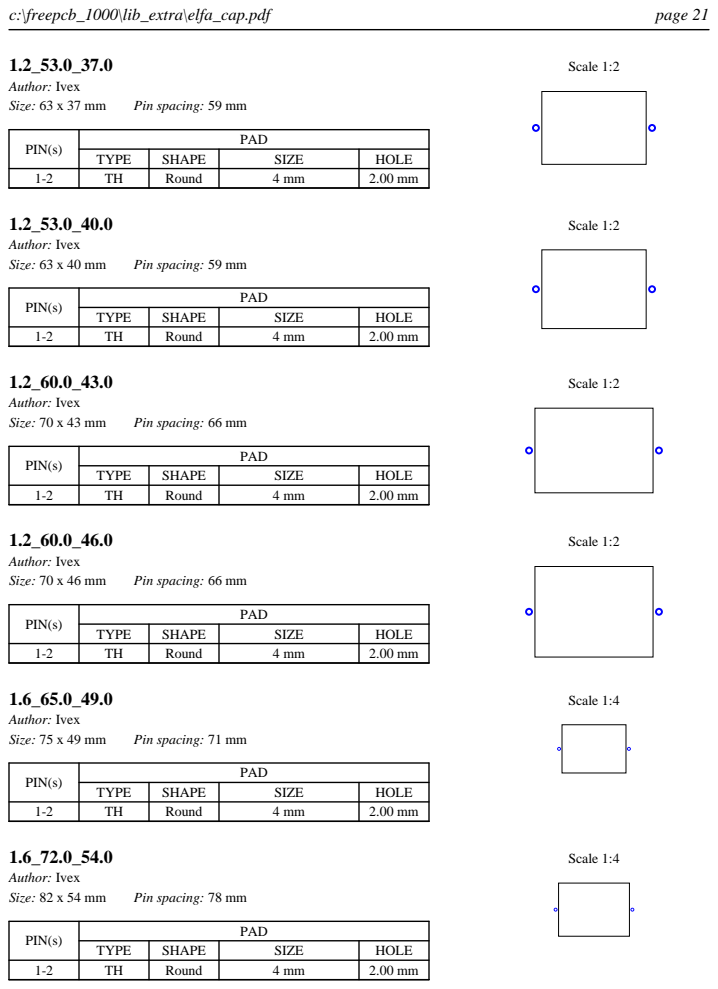
[picture p50: page 21]
Author: Ivex; Size: 63 x 37 mm; Pin spacing: 59 mm; Scale 1:2; Size: 63 x 40 mm; Size: 70 x 43 mm; Pin spacing: 66 mm; Size: 70 x 46 mm; Size: 75 x 49 mm; Pin spacing: 71 mm; Scale 1:4; Size: 82 x 54 mm; Pin spacing: 78 mm

PIN(s) | PAD

TYPE | SHAPE | SIZE | HOLE

1-2 | TH | Round | 4 mm | 2.00 mm

1.6_84.0_60.0

1.6_115.0_63.0

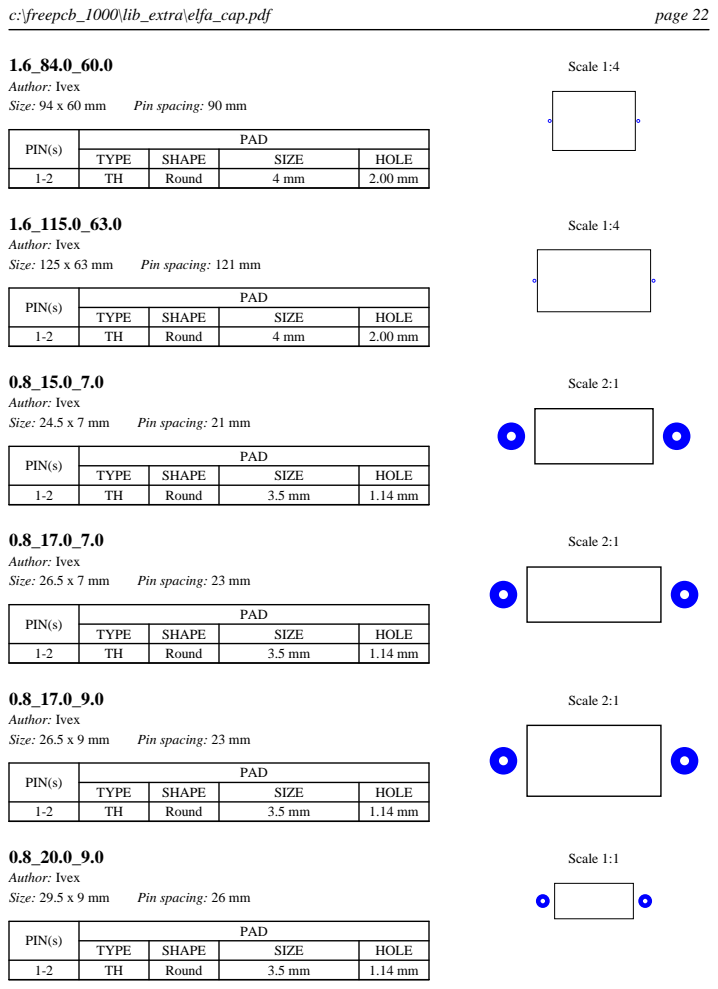
[picture p51: page 22]
Author: Ivex; Size: 94 x 60 mm; Pin spacing: 90 mm; Scale 1:4; Size: 125 x 63 mm; Pin spacing: 121 mm; Size: 24.5 x 7 mm; Pin spacing: 21 mm; Scale 2:1; Size: 26.5 x 7 mm; Pin spacing: 23 mm; Size: 26.5 x 9 mm; Size: 29.5 x 9 mm; Pin spacing: 26 mm; Scale 1:1

PIN(s) | PAD

TYPE | SHAPE | SIZE | HOLE

1-2 | TH | Round | 4 mm | 2.00 mm

1-2 | TH | Round | 3.5 mm | 1.14 mm

0.8_20.0_10.0

0.8_23.0_13.0

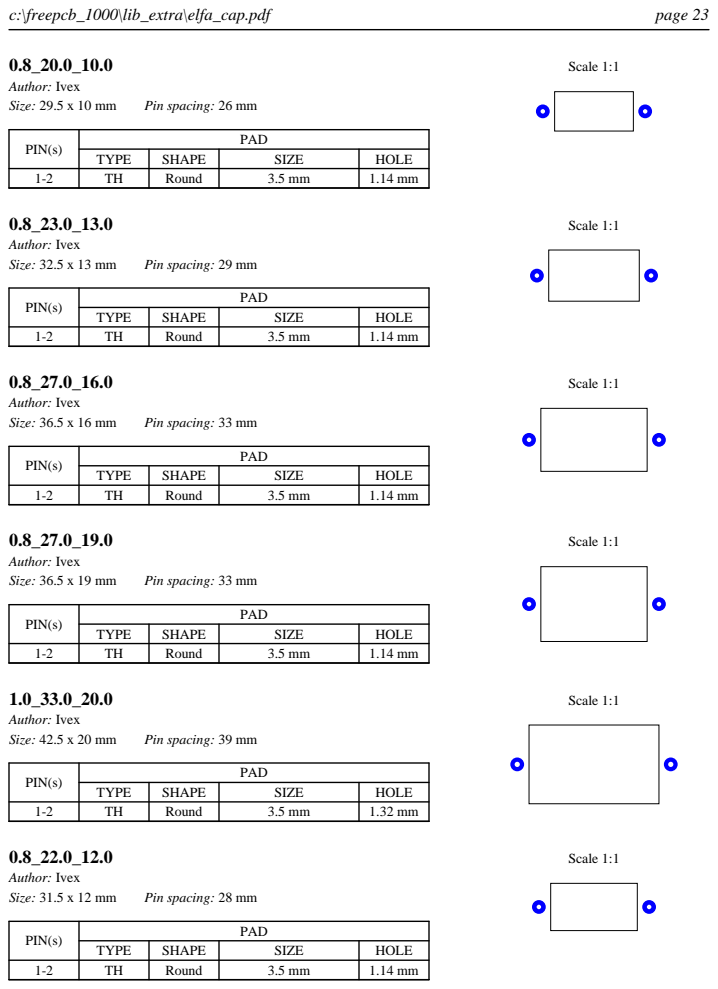
[picture p52: page 23]
Author: Ivex; Size: 29.5 x 10 mm; Pin spacing: 26 mm; Scale 1:1; Size: 32.5 x 13 mm; Pin spacing: 29 mm; Size: 36.5 x 16 mm; Pin spacing: 33 mm; Size: 36.5 x 19 mm; Size: 42.5 x 20 mm; Pin spacing: 39 mm; Size: 31.5 x 12 mm; Pin spacing: 28 mm

PIN(s) | PAD

TYPE | SHAPE | SIZE | HOLE

1-2 | TH | Round | 3.5 mm | 1.14 mm

1-2 | TH | Round | 3.5 mm | 1.32 mm

0.8_25.0_15.0

0.8_25.0_17.0

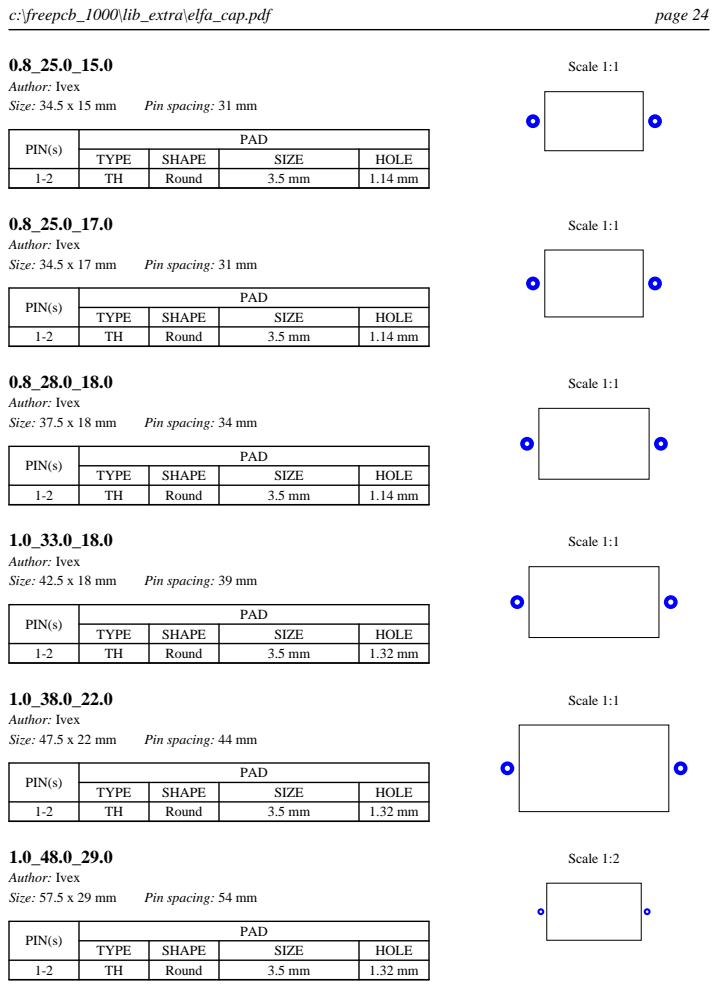
[picture p53: page 24]
Author: Ivex; Size: 34.5 x 15 mm; Pin spacing: 31 mm; Scale 1:1; Size: 34.5 x 17 mm; Size: 37.5 x 18 mm; Pin spacing: 34 mm; Size: 42.5 x 18 mm; Pin spacing: 39 mm; Size: 47.5 x 22 mm; Pin spacing: 44 mm; Size: 57.5 x 29 mm; Pin spacing: 54 mm; Scale 1:2

PIN(s) | PAD

TYPE | SHAPE | SIZE | HOLE

1-2 | TH | Round | 3.5 mm | 1.14 mm

1-2 | TH | Round | 3.5 mm | 1.32 mm

0.6_14.0_6.0

0.7_14.0_7.0

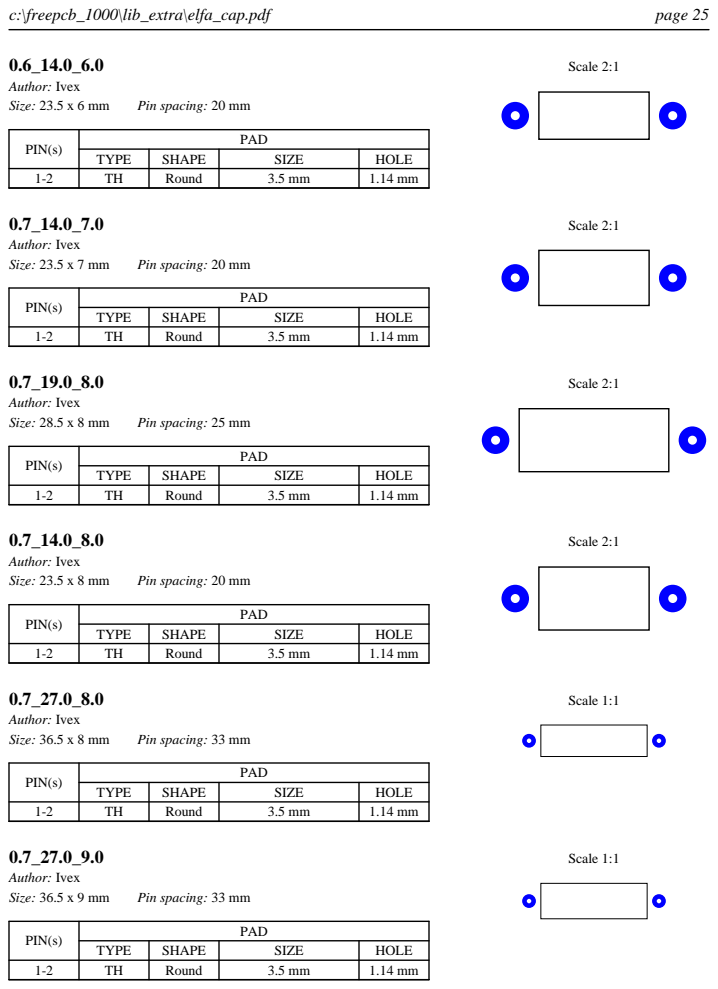
[picture p54: page 25]
Author: Ivex; Size: 23.5 x 6 mm; Pin spacing: 20 mm; Size: 23.5 x 7 mm; Scale 2:1; Size: 28.5 x 8 mm; Pin spacing: 25 mm; Size: 23.5 x 8 mm; Size: 36.5 x 8 mm; Pin spacing: 33 mm; Scale 1:1; Size: 36.5 x 9 mm

PIN(s) | PAD

TYPE | SHAPE | SIZE | HOLE

1-2 | TH | Round | 3.5 mm | 1.14 mm

0.8_27.0_10.0

0.8_27.0_11.0

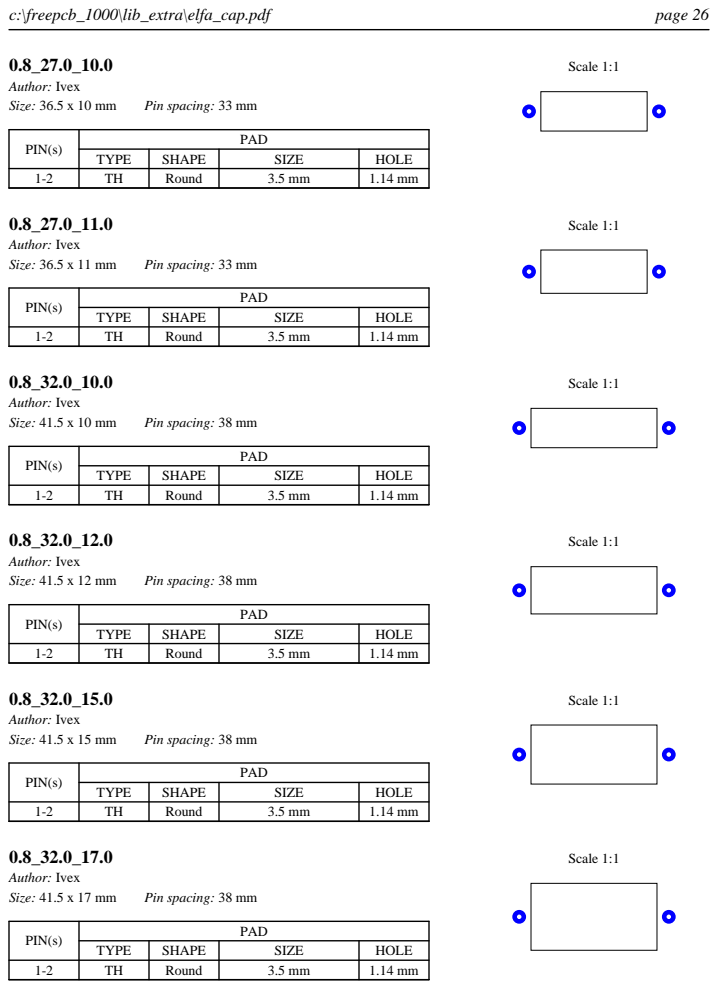
[picture p55: page 26]
Author: Ivex; Size: 36.5 x 10 mm; Pin spacing: 33 mm; Scale 1:1; Size: 36.5 x 11 mm; Size: 41.5 x 10 mm; Pin spacing: 38 mm; Size: 41.5 x 12 mm; Size: 41.5 x 15 mm; Size: 41.5 x 17 mm

PIN(s) | PAD

TYPE | SHAPE | SIZE | HOLE

1-2 | TH | Round | 3.5 mm | 1.14 mm

0.8_32.0_20.0

## RIFA_PMR209A

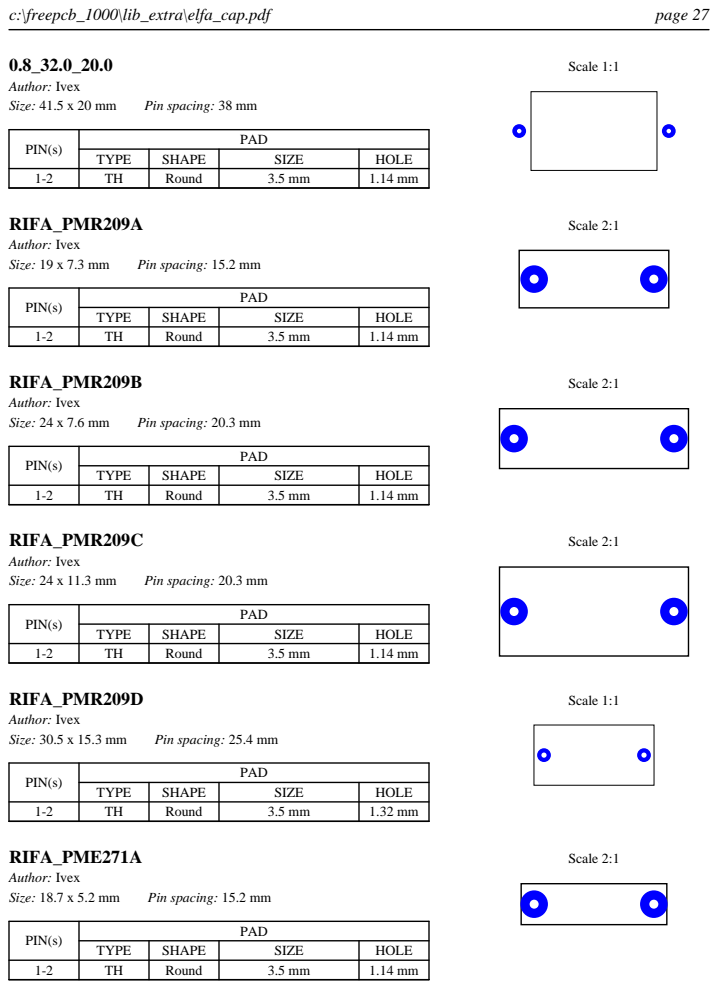
[picture p56: page 27]
Author: Ivex; Size: 41.5 x 20 mm; Pin spacing: 38 mm; Scale 1:1; Size: 19 x 7.3 mm; Pin spacing: 15.2 mm; Scale 2:1; RIFA_PMR209B; Size: 24 x 7.6 mm; Pin spacing: 20.3 mm; RIFA_PMR209C; Size: 24 x 11.3 mm; RIFA_PMR209D; Size: 30.5 x 15.3 mm; Pin spacing: 25.4 mm; RIFA_PME271A; Size: 18.7 x 5.2 mm

PIN(s) | PAD

TYPE | SHAPE | SIZE | HOLE

1-2 | TH | Round | 3.5 mm | 1.14 mm

1-2 | TH | Round | 3.5 mm | 1.32 mm

## RIFA_PME271B

## RIFA_PME271C

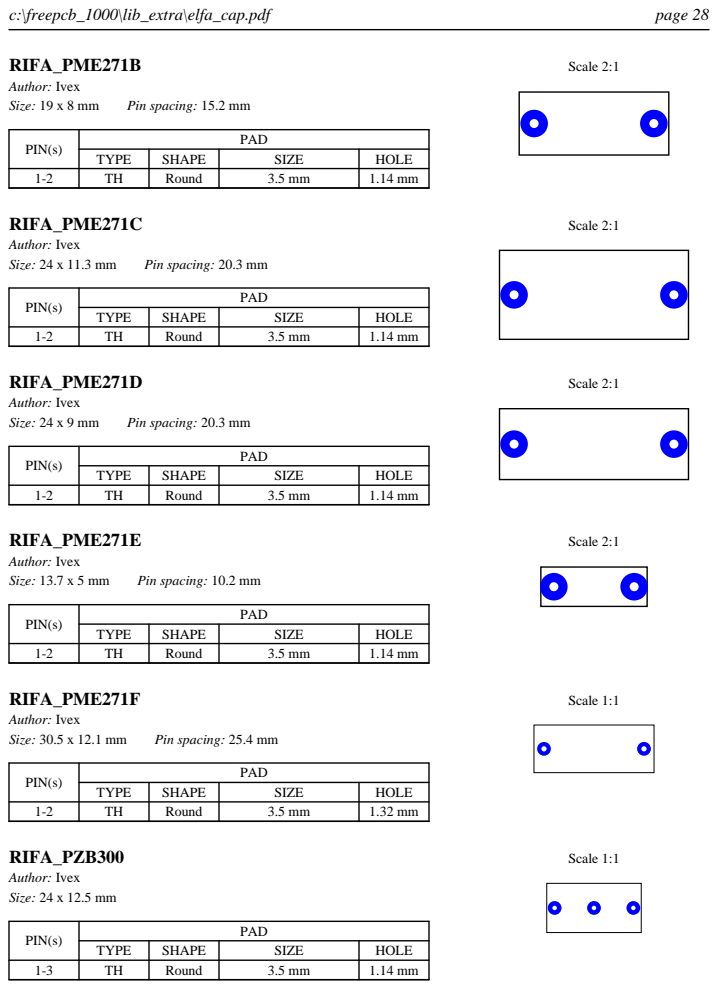
[picture p57: page 28]
Author: Ivex; Size: 19 x 8 mm; Pin spacing: 15.2 mm; Size: 24 x 11.3 mm; Pin spacing: 20.3 mm; Scale 2:1; RIFA_PME271D; Size: 24 x 9 mm; RIFA_PME271E; Size: 13.7 x 5 mm; Pin spacing: 10.2 mm; RIFA_PME271F; Size: 30.5 x 12.1 mm; Pin spacing: 25.4 mm; Scale 1:1; RIFA_PZB300; Author: Ivex Size: 24 x 12.5 mm

PIN(s) | PAD

TYPE | SHAPE | SIZE | HOLE

1-2 | TH | Round | 3.5 mm | 1.14 mm

1-2 | TH | Round | 3.5 mm | 1.32 mm

1-3 | TH | Round | 3.5 mm | 1.14 mm

## MUR_DSS306

## MUR_DSS710

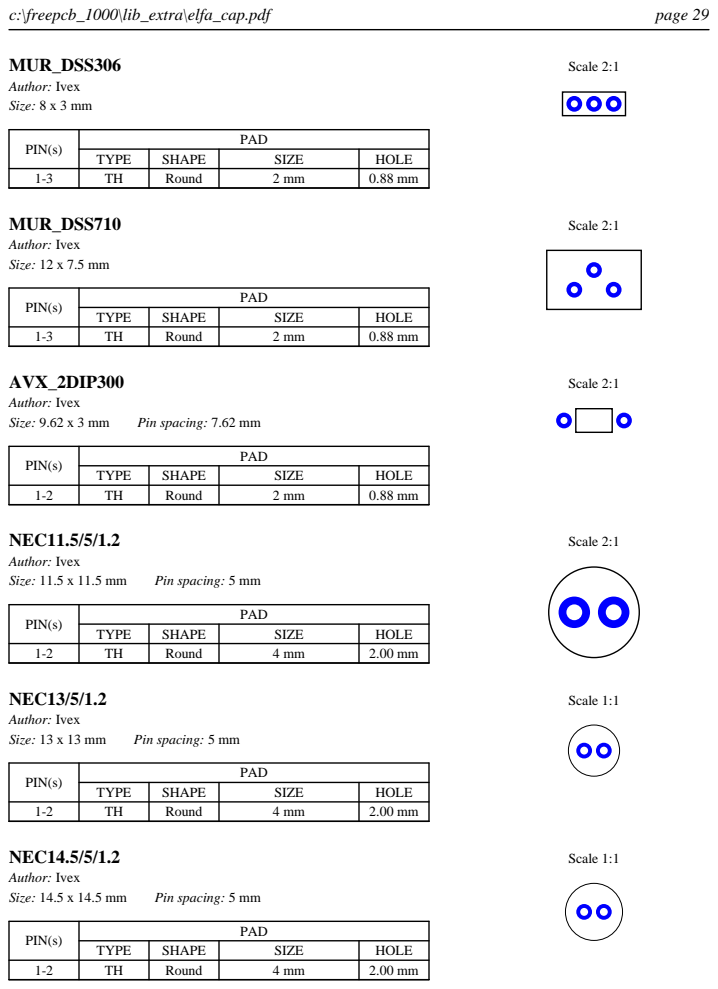
[picture p58: page 29]
Author: Ivex Size: 8 x 3 mm; Author: Ivex Size: 12 x 7.5 mm; Scale 2:1; AVX_2DIP300; Author: Ivex; Size: 9.62 x 3 mm; Pin spacing: 7.62 mm; NEC11.5/5/1.2; Size: 11.5 x 11.5 mm; Pin spacing: 5 mm; NEC13/5/1.2; Size: 13 x 13 mm; Scale 1:1; NEC14.5/5/1.2; Size: 14.5 x 14.5 mm

PIN(s) | PAD

TYPE | SHAPE | SIZE | HOLE

1-3 | TH | Round | 2 mm | 0.88 mm

1-2 | TH | Round | 2 mm | 0.88 mm

1-2 | TH | Round | 4 mm | 2.00 mm

## NEC16.5/5/1.2

NEC21.5/7.5/1.

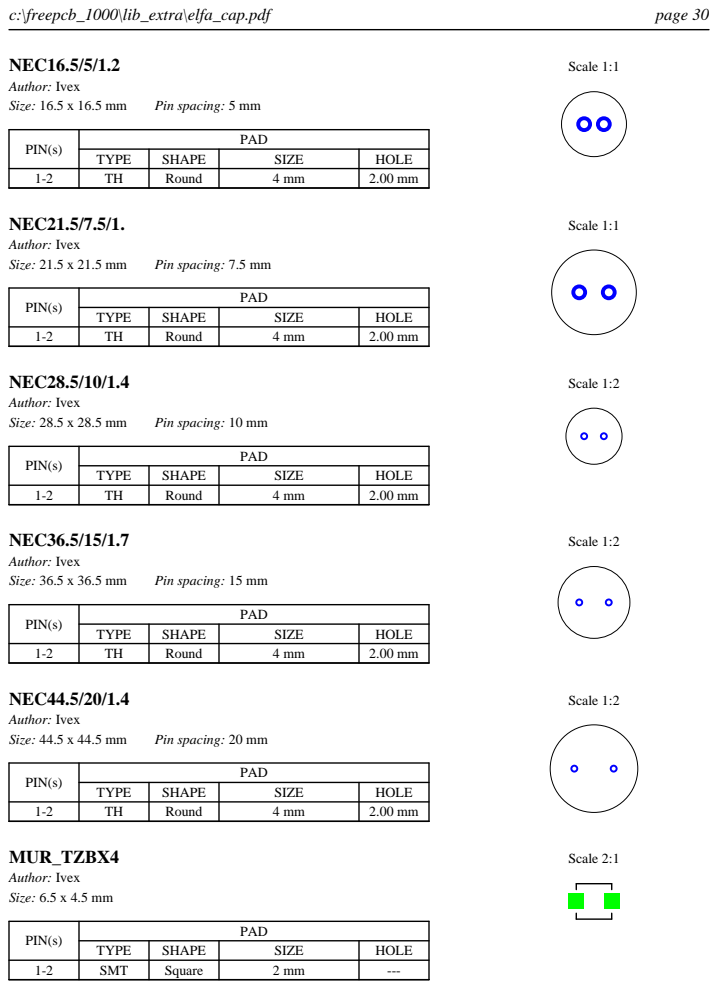
[picture p59: page 30]
Author: Ivex; Size: 16.5 x 16.5 mm; Pin spacing: 5 mm; Scale 1:1; Size: 21.5 x 21.5 mm; Pin spacing: 7.5 mm; NEC28.5/10/1.4; Size: 28.5 x 28.5 mm; Pin spacing: 10 mm; Scale 1:2; NEC36.5/15/1.7; Size: 36.5 x 36.5 mm; Pin spacing: 15 mm; NEC44.5/20/1.4; Size: 44.5 x 44.5 mm; Pin spacing: 20 mm; MUR_TZBX4; Author: Ivex Size: 6.5 x 4.5 mm; Scale 2:1

PIN(s) | PAD

TYPE | SHAPE | SIZE | HOLE

1-2 | TH | Round | 4 mm | 2.00 mm

1-2 | SMT | Square | 2 mm | ---

## STET_7S

## STET_10S

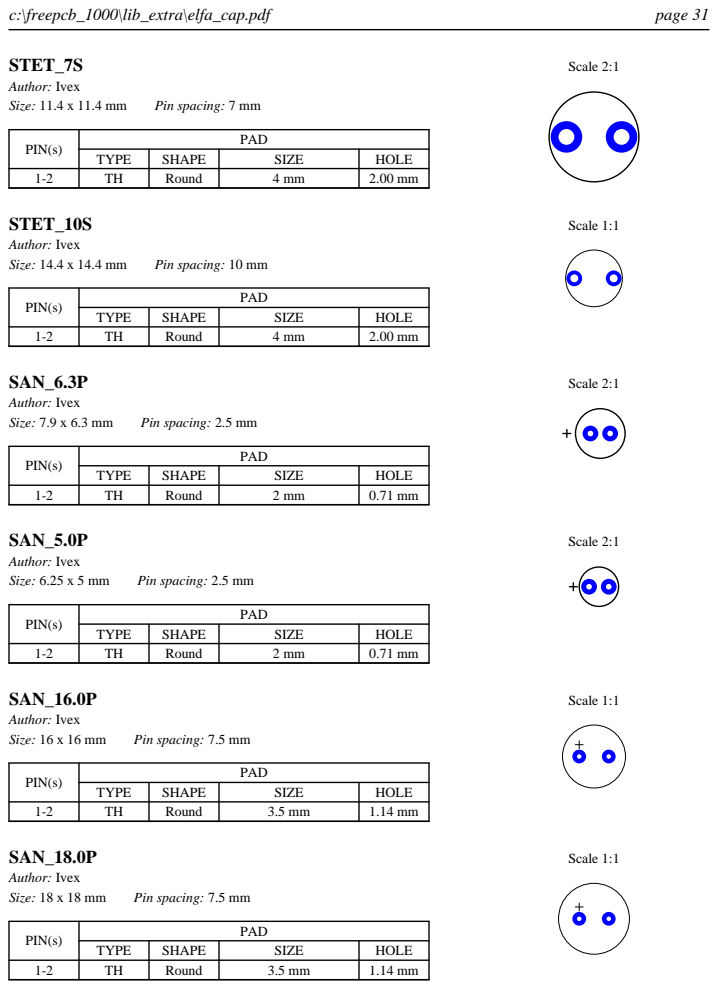
[picture p60: page 31]
Author: Ivex; Size: 11.4 x 11.4 mm; Pin spacing: 7 mm; Size: 14.4 x 14.4 mm; Pin spacing: 10 mm; Scale 1:1; SAN_6.3P; Size: 7.9 x 6.3 mm; Pin spacing: 2.5 mm; Scale 2:1; SAN_5.0P; Size: 6.25 x 5 mm; SAN_16.0P; Size: 16 x 16 mm; Pin spacing: 7.5 mm; SAN_18.0P; Size: 18 x 18 mm

PIN(s) | PAD

TYPE | SHAPE | SIZE | HOLE

1-2 | TH | Round | 4 mm | 2.00 mm

1-2 | TH | Round | 2 mm | 0.71 mm

1-2 | TH | Round | 3.5 mm | 1.14 mm

## SAN_C/SV4.0

## SAN_C/SV5.0

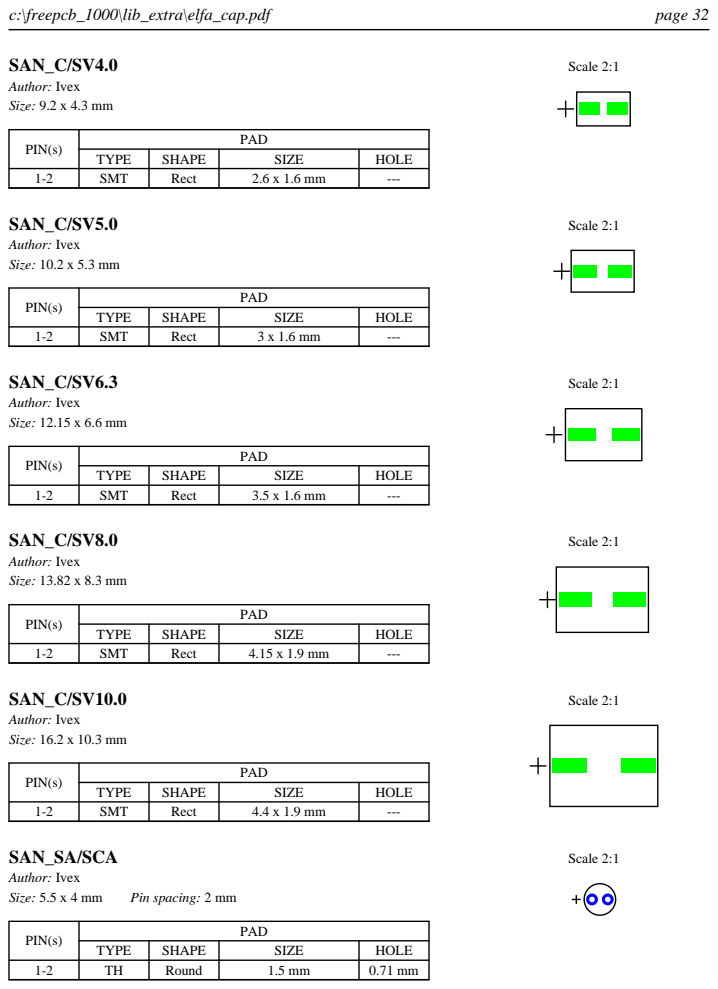
[picture p61: page 32]
Author: Ivex Size: 9.2 x 4.3 mm; Author: Ivex Size: 10.2 x 5.3 mm; Scale 2:1; SAN_C/SV6.3; Author: Ivex Size: 12.15 x 6.6 mm; SAN_C/SV8.0; Author: Ivex Size: 13.82 x 8.3 mm; SAN_C/SV10.0; Author: Ivex Size: 16.2 x 10.3 mm; SAN_SA/SCA; Author: Ivex; Size: 5.5 x 4 mm; Pin spacing: 2 mm

PIN(s) | PAD

TYPE | SHAPE | SIZE | HOLE

1-2 | SMT | Rect | 2.6 x 1.6 mm | ---

1-2 | SMT | Rect | 3 x 1.6 mm | ---

1-2 | SMT | Rect | 3.5 x 1.6 mm | ---

1-2 | SMT | Rect | 4.15 x 1.9 mm | ---

1-2 | SMT | Rect | 4.4 x 1.9 mm | ---

1-2 | TH | Round | 1.5 mm | 0.71 mm

## SAN_SA/SCB

## SAN_SA/SCC

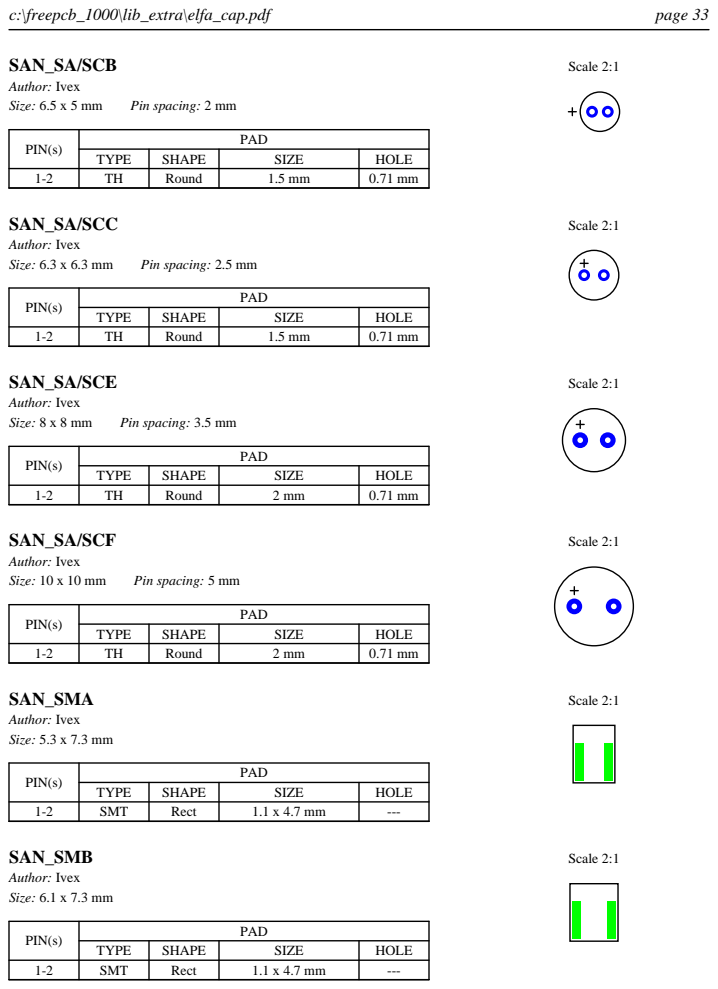
[picture p62: page 33]
Author: Ivex; Size: 6.5 x 5 mm; Pin spacing: 2 mm; Size: 6.3 x 6.3 mm; Pin spacing: 2.5 mm; Scale 2:1; SAN_SA/SCE; Size: 8 x 8 mm; Pin spacing: 3.5 mm; SAN_SA/SCF; Size: 10 x 10 mm; Pin spacing: 5 mm; SAN_SMA; Author: Ivex Size: 5.3 x 7.3 mm; SAN_SMB; Author: Ivex Size: 6.1 x 7.3 mm

PIN(s) | PAD

TYPE | SHAPE | SIZE | HOLE

1-2 | TH | Round | 1.5 mm | 0.71 mm

1-2 | TH | Round | 2 mm | 0.71 mm

1-2 | SMT | Rect | 1.1 x 4.7 mm | ---

## SAN_SMC

## SAN_SMD

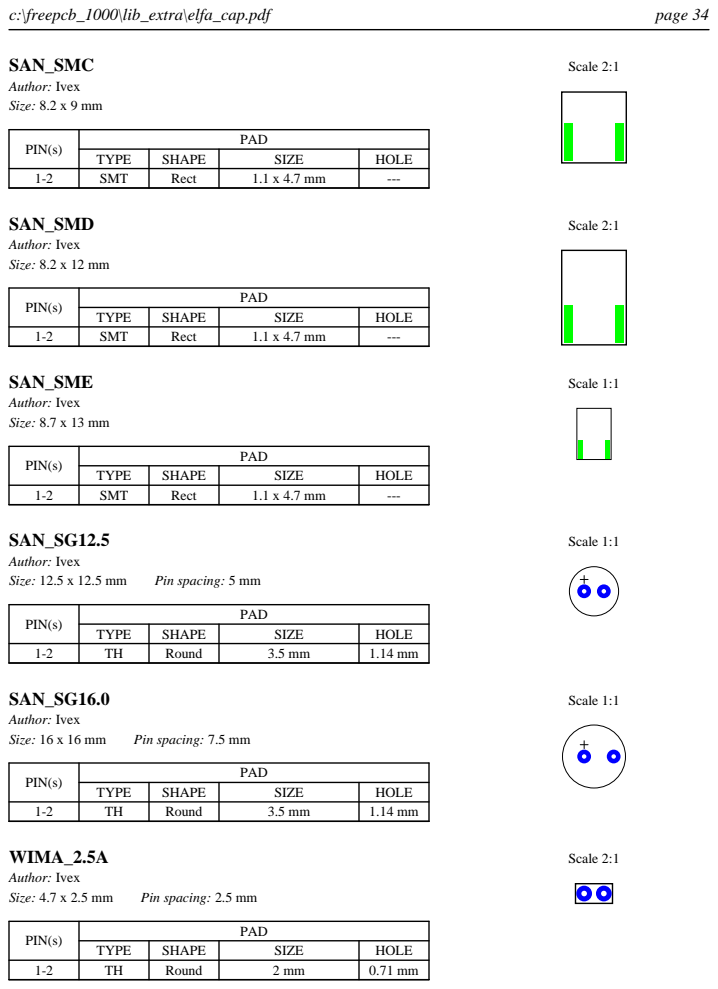
[picture p63: page 34]
Author: Ivex Size: 8.2 x 9 mm; Author: Ivex Size: 8.2 x 12 mm; Scale 2:1; SAN_SME; Author: Ivex Size: 8.7 x 13 mm; Scale 1:1; SAN_SG12.5; Author: Ivex; Size: 12.5 x 12.5 mm; Pin spacing: 5 mm; SAN_SG16.0; Size: 16 x 16 mm; Pin spacing: 7.5 mm; WIMA_2.5A; Size: 4.7 x 2.5 mm; Pin spacing: 2.5 mm

PIN(s) | PAD

TYPE | SHAPE | SIZE | HOLE

1-2 | SMT | Rect | 1.1 x 4.7 mm | ---

1-2 | TH | Round | 3.5 mm | 1.14 mm

1-2 | TH | Round | 2 mm | 0.71 mm

## WIMA_2.5B

## WIMA_2.5C

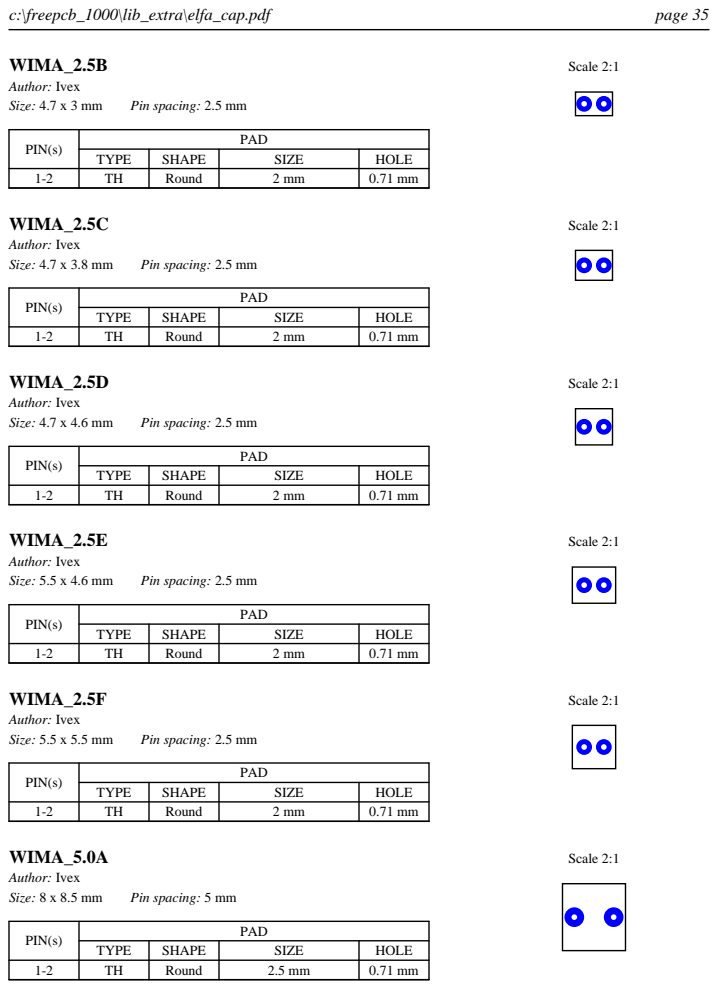
[picture p64: page 35]
Author: Ivex; Size: 4.7 x 3 mm; Pin spacing: 2.5 mm; Size: 4.7 x 3.8 mm; Scale 2:1; WIMA_2.5D; Size: 4.7 x 4.6 mm; WIMA_2.5E; Size: 5.5 x 4.6 mm; WIMA_2.5F; Size: 5.5 x 5.5 mm; WIMA_5.0A; Size: 8 x 8.5 mm; Pin spacing: 5 mm

PIN(s) | PAD

TYPE | SHAPE | SIZE | HOLE

1-2 | TH | Round | 2 mm | 0.71 mm

1-2 | TH | Round | 2.5 mm | 0.71 mm

## WIMA_5.0B

## WIMA_5.0C

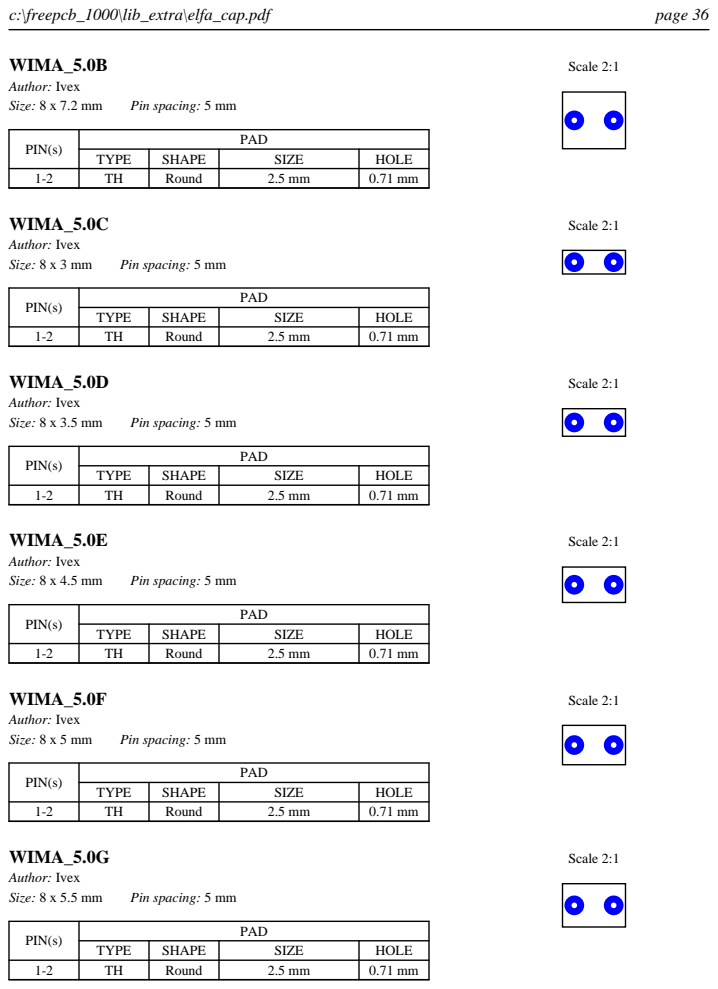
[picture p65: page 36]
Author: Ivex; Size: 8 x 7.2 mm; Pin spacing: 5 mm; Size: 8 x 3 mm; Scale 2:1; WIMA_5.0D; Size: 8 x 3.5 mm; WIMA_5.0E; Size: 8 x 4.5 mm; WIMA_5.0F; Size: 8 x 5 mm; WIMA_5.0G; Size: 8 x 5.5 mm

PIN(s) | PAD

TYPE | SHAPE | SIZE | HOLE

1-2 | TH | Round | 2.5 mm | 0.71 mm

## WIMA_5.0H

## WIMA_7.5A

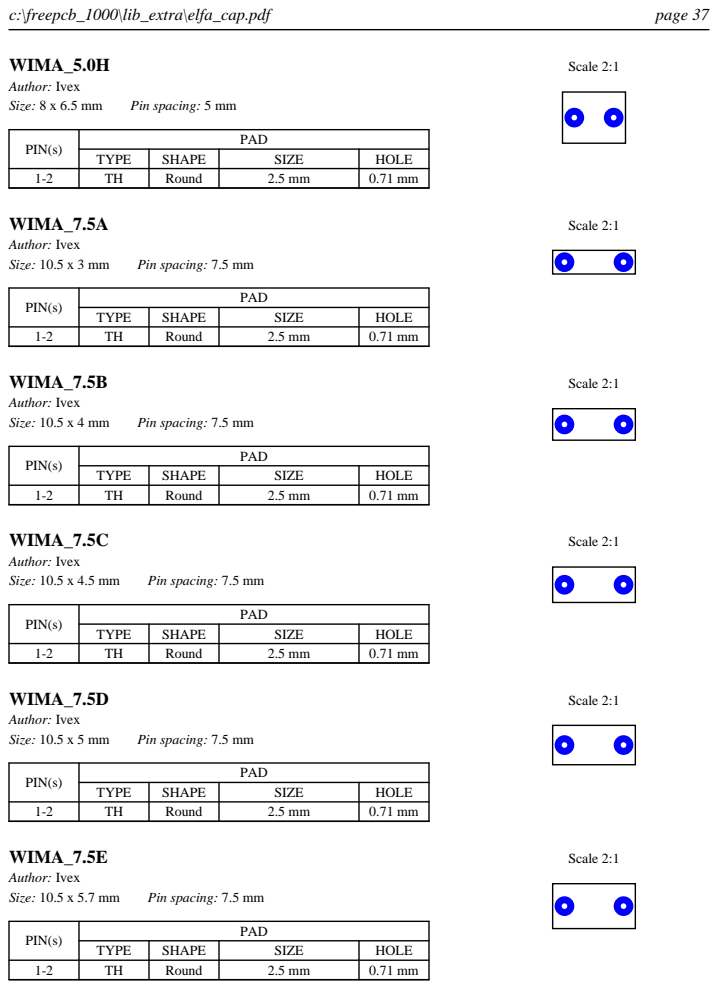
[picture p66: page 37]
Author: Ivex; Size: 8 x 6.5 mm; Pin spacing: 5 mm; Size: 10.5 x 3 mm; Pin spacing: 7.5 mm; Scale 2:1; WIMA_7.5B; Size: 10.5 x 4 mm; WIMA_7.5C; Size: 10.5 x 4.5 mm; WIMA_7.5D; Size: 10.5 x 5 mm; WIMA_7.5E; Size: 10.5 x 5.7 mm

PIN(s) | PAD

TYPE | SHAPE | SIZE | HOLE

1-2 | TH | Round | 2.5 mm | 0.71 mm

## WIMA_10A

## WIMA_10B

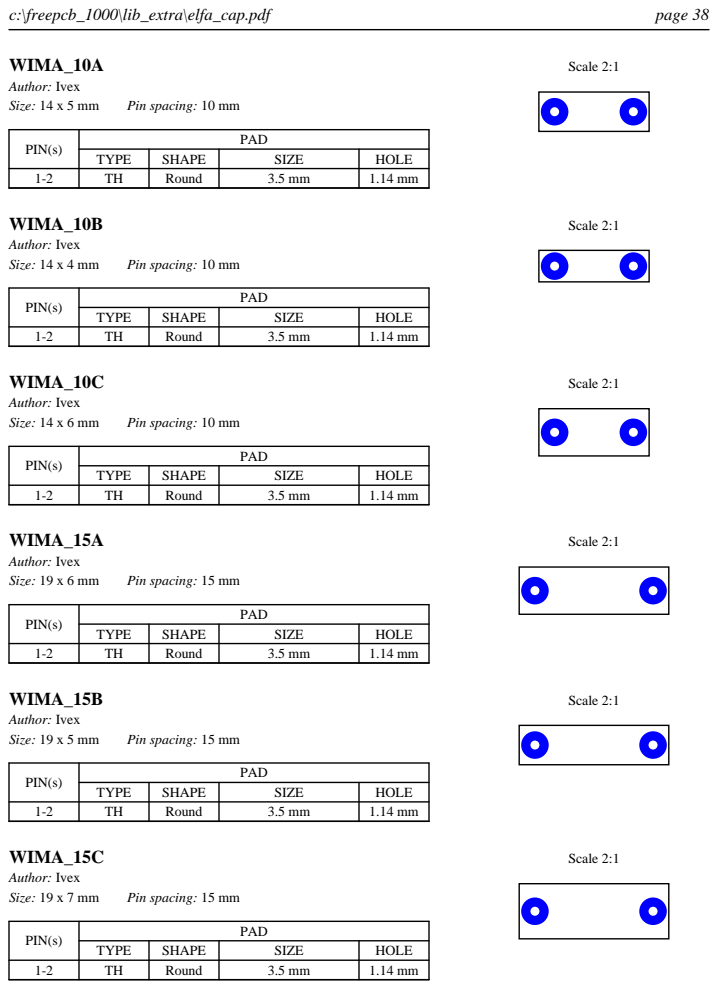
[picture p67: page 38]
Author: Ivex; Size: 14 x 5 mm; Pin spacing: 10 mm; Size: 14 x 4 mm; Scale 2:1; WIMA_10C; Size: 14 x 6 mm; WIMA_15A; Size: 19 x 6 mm; Pin spacing: 15 mm; WIMA_15B; Size: 19 x 5 mm; WIMA_15C; Size: 19 x 7 mm

PIN(s) | PAD

TYPE | SHAPE | SIZE | HOLE

1-2 | TH | Round | 3.5 mm | 1.14 mm

## WIMA_15D

## WIMA_15E

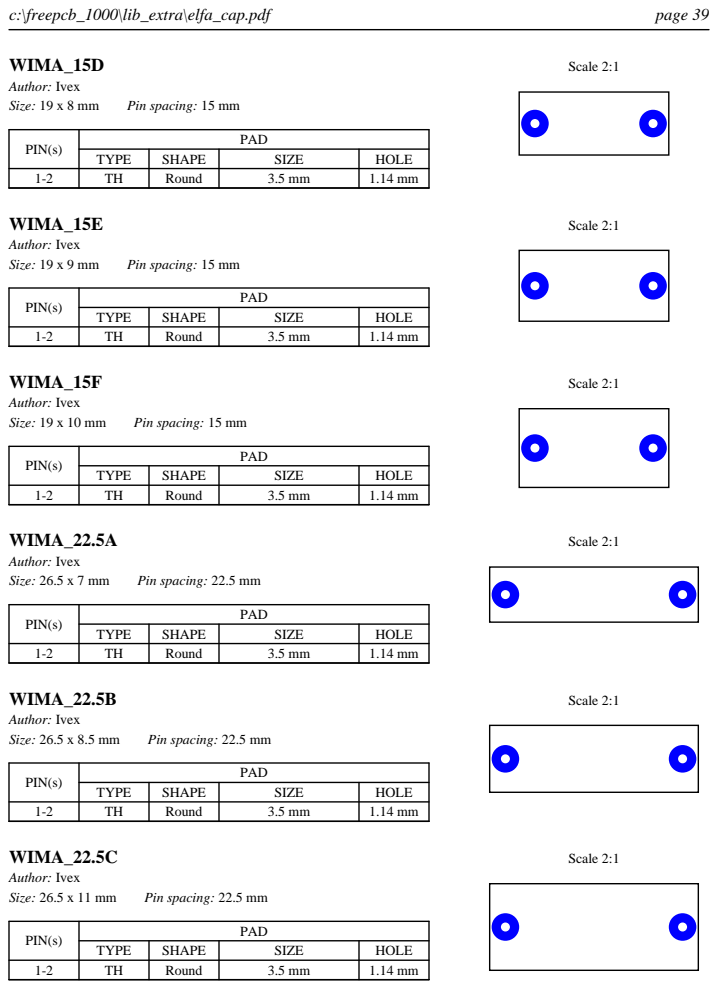
[picture p68: page 39]
Author: Ivex; Size: 19 x 8 mm; Pin spacing: 15 mm; Size: 19 x 9 mm; Scale 2:1; WIMA_15F; Size: 19 x 10 mm; WIMA_22.5A; Size: 26.5 x 7 mm; Pin spacing: 22.5 mm; WIMA_22.5B; Size: 26.5 x 8.5 mm; WIMA_22.5C; Size: 26.5 x 11 mm

PIN(s) | PAD

TYPE | SHAPE | SIZE | HOLE

1-2 | TH | Round | 3.5 mm | 1.14 mm

## WIMA_22.5D

## WIMA_22.5E

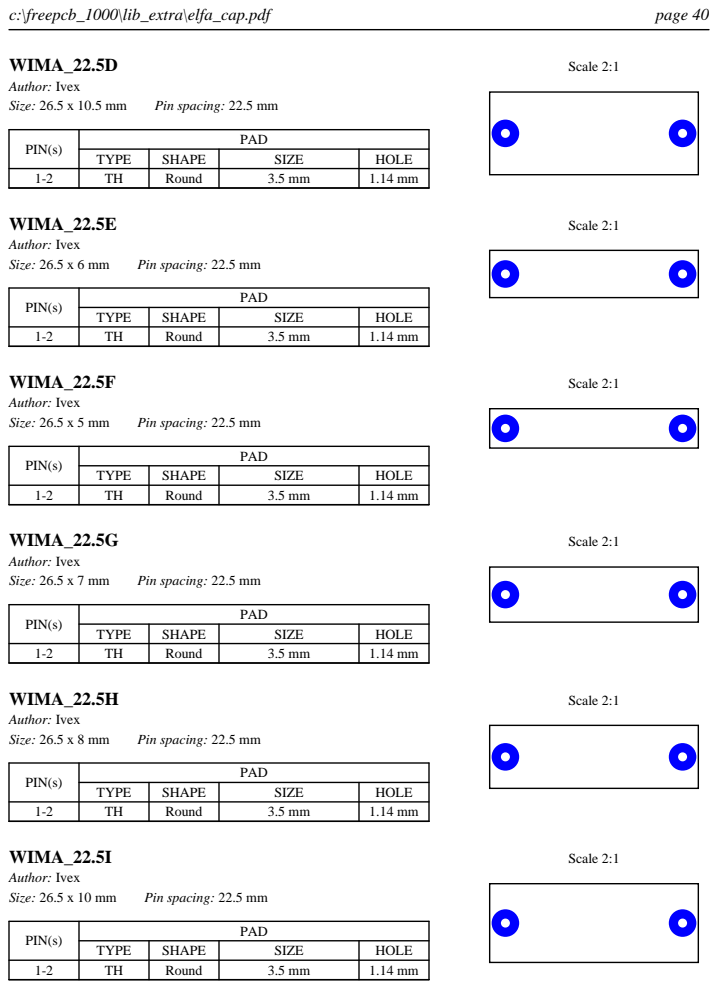
[picture p69: page 40]
Author: Ivex; Size: 26.5 x 10.5 mm; Pin spacing: 22.5 mm; Size: 26.5 x 6 mm; Scale 2:1; WIMA_22.5F; Size: 26.5 x 5 mm; WIMA_22.5G; Size: 26.5 x 7 mm; WIMA_22.5H; Size: 26.5 x 8 mm; WIMA_22.5I; Size: 26.5 x 10 mm

PIN(s) | PAD

TYPE | SHAPE | SIZE | HOLE

1-2 | TH | Round | 3.5 mm | 1.14 mm

## WIMA_22.5J

## WIMA_27.5A

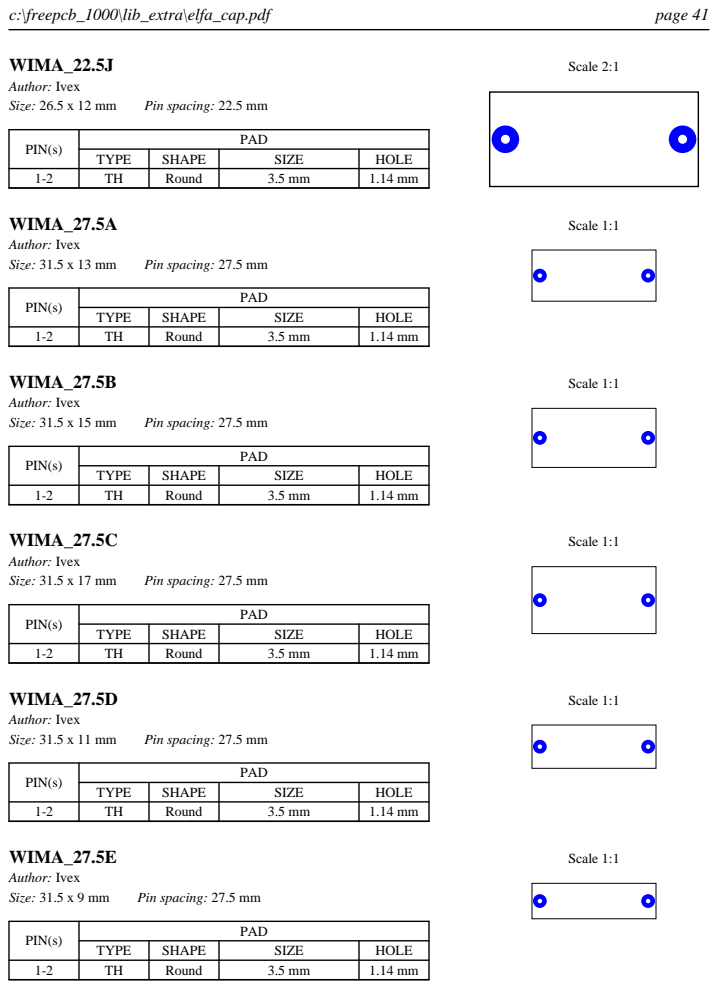
[picture p70: page 41]
Author: Ivex; Size: 26.5 x 12 mm; Pin spacing: 22.5 mm; Size: 31.5 x 13 mm; Pin spacing: 27.5 mm; Scale 1:1; WIMA_27.5B; Size: 31.5 x 15 mm; WIMA_27.5C; Size: 31.5 x 17 mm; WIMA_27.5D; Size: 31.5 x 11 mm; WIMA_27.5E; Size: 31.5 x 9 mm

PIN(s) | PAD

TYPE | SHAPE | SIZE | HOLE

1-2 | TH | Round | 3.5 mm | 1.14 mm

## WIMA_27.5F

## WIMA_37.5A

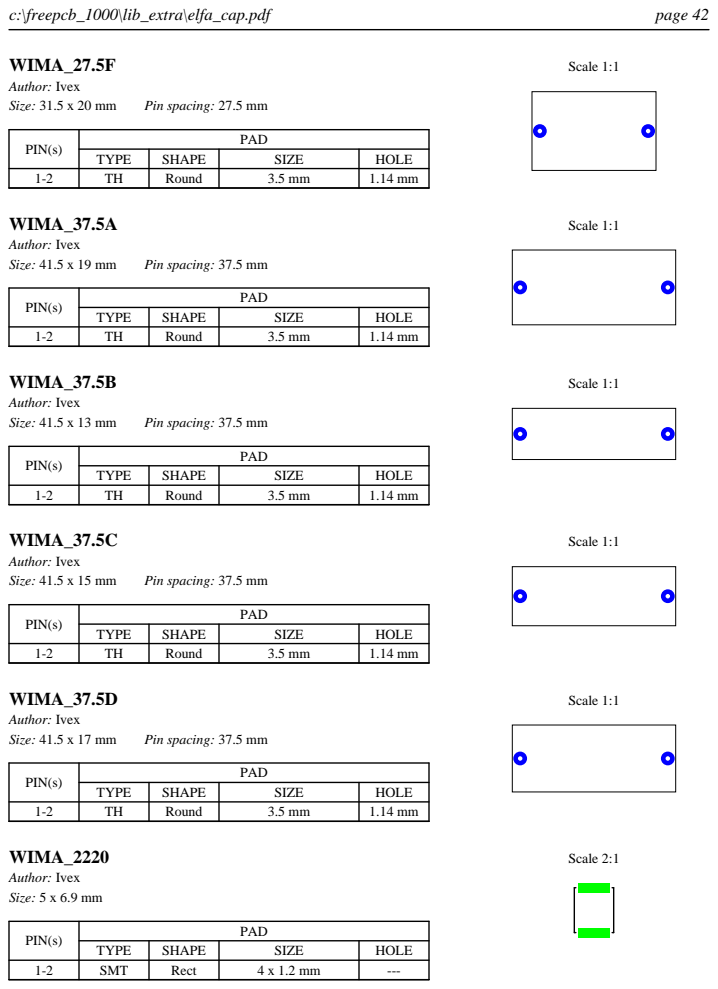
[picture p71: page 42]
Author: Ivex; Size: 31.5 x 20 mm; Pin spacing: 27.5 mm; Scale 1:1; Size: 41.5 x 19 mm; Pin spacing: 37.5 mm; WIMA_37.5B; Size: 41.5 x 13 mm; WIMA_37.5C; Size: 41.5 x 15 mm; WIMA_37.5D; Size: 41.5 x 17 mm; WIMA_2220; Author: Ivex Size: 5 x 6.9 mm; Scale 2:1

PIN(s) | PAD

TYPE | SHAPE | SIZE | HOLE

1-2 | TH | Round | 3.5 mm | 1.14 mm

1-2 | SMT | Rect | 4 x 1.2 mm | ---

## WIMA_2824

Author: Ivex
Size: 6 x 8.9 mm
PIN(s) | PAD
TYPE | SHAPE | SIZE | HOLE
1-2 | SMT | Rect | 4 x 1.2 mm | ---
