PingvinOpenTag/LTAscetic/release_2(LCD,Joystck,TouchMemory,Reload,Antichiter,IrPowerControl,BattaryControl)/hardware/pcb/FreePCB/lib_extra/elfa_chk.pdf

0.8_10.0_6.0

0.8_10.0_7.0

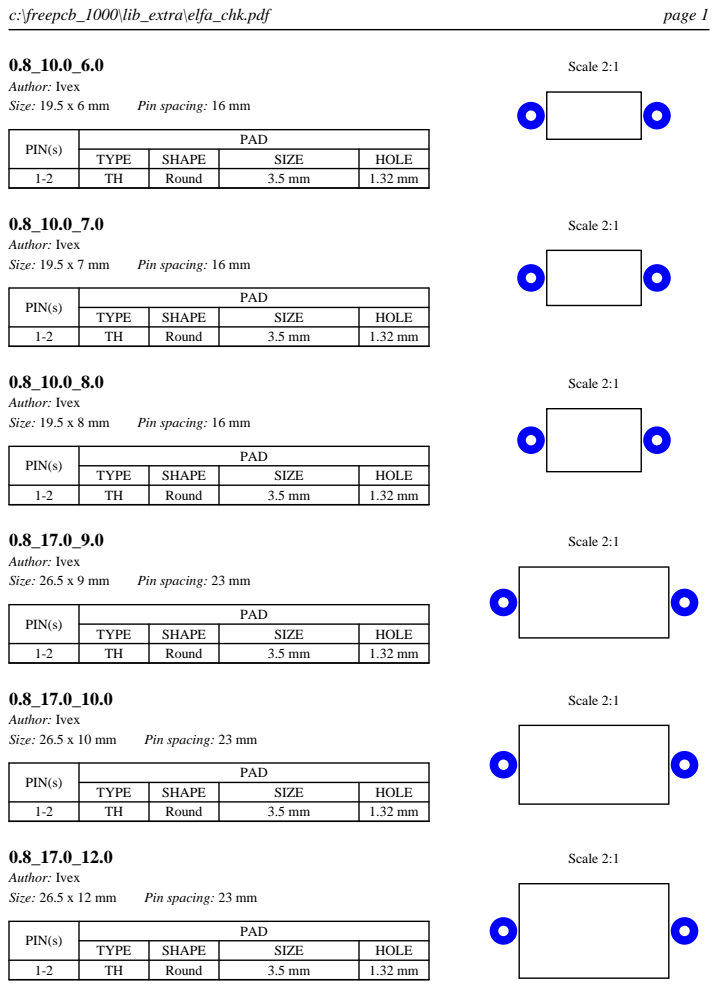
[picture p72: page 1]
c:\freepcb_1000\lib_extra\elfa_chk.pdf; page 1; Author: Ivex; Size: 19.5 x 6 mm; Pin spacing: 16 mm; Scale 2:1; Size: 19.5 x 7 mm; Size: 19.5 x 8 mm; Size: 26.5 x 9 mm; Pin spacing: 23 mm; Size: 26.5 x 10 mm; Size: 26.5 x 12 mm

PIN(s) | PAD

TYPE | SHAPE | SIZE | HOLE

1-2 | TH | Round | 3.5 mm | 1.32 mm

## SD_75

## P646/TC

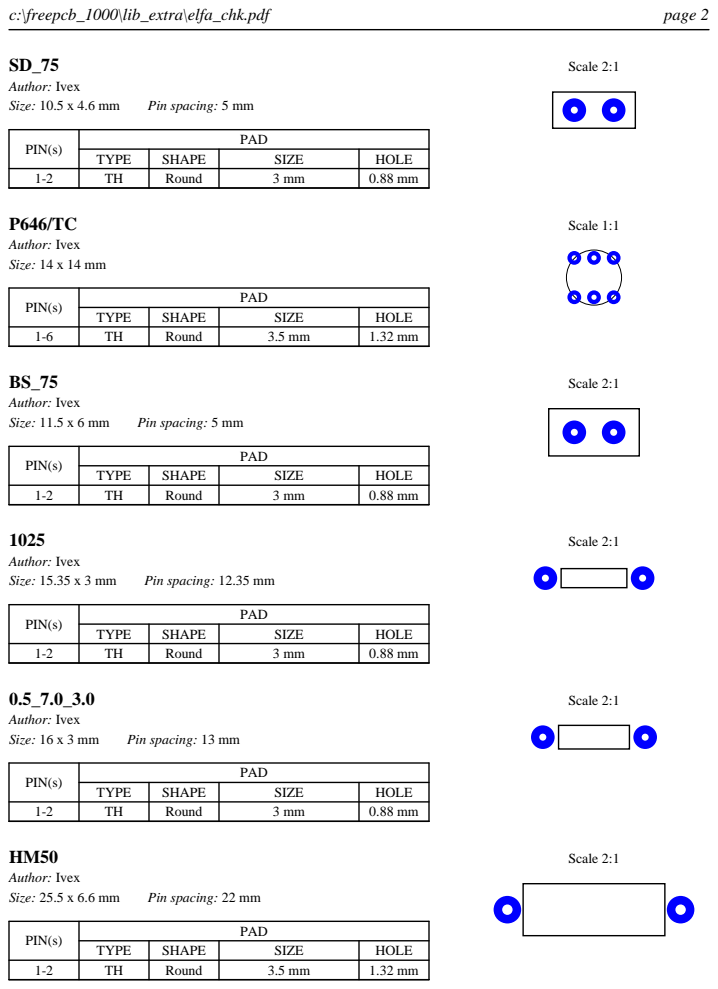
[picture p73: page 2]
Author: Ivex; Size: 10.5 x 4.6 mm; Pin spacing: 5 mm; Author: Ivex Size: 14 x 14 mm; Scale 1:1; Size: 11.5 x 6 mm; Scale 2:1; Size: 15.35 x 3 mm; Pin spacing: 12.35 mm; Size: 16 x 3 mm; Pin spacing: 13 mm; Size: 25.5 x 6.6 mm; Pin spacing: 22 mm

PIN(s) | PAD

TYPE | SHAPE | SIZE | HOLE

1-2 | TH | Round | 3 mm | 0.88 mm

1-6 | TH | Round | 3.5 mm | 1.32 mm

1-2 | TH | Round | 3.5 mm | 1.32 mm

## LQH4N

Author: Ivex
Size: 5.6 x 4.1 mm
PIN(s) | PAD
TYPE | SHAPE | SIZE | HOLE
1-2 | SMT | Rect | 2 x 3.5 mm | ---

## LPC4045

Author: Ivex
Size: 6.1 x 4.1 mm
PIN(s) | PAD
TYPE | SHAPE | SIZE | HOLE
1-2 | SMT | Rect | 2 x 3.5 mm | ---

Scale 2:1

## SDR0906

Author: Ivex
Size: 10.4 x 14.6 mm
PIN(s) | PAD
TYPE | SHAPE | SIZE | HOLE
1-8 | SMT | Square | 2 mm | ---

Scale 1:1

## BCL_322522

Author: Ivex
Size: 4.2 x 3.6 mm
PIN(s) | PAD
TYPE | SHAPE | SIZE | HOLE
1-2 | SMT | Rect | 1 x 3 mm | ---

Scale 2:1

## BCL_453232

Author: Ivex
Size: 6.1 x 4.6 mm
PIN(s) | PAD
TYPE | SHAPE | SIZE | HOLE
1-2 | SMT | Rect | 2 x 4 mm | ---

Scale 2:1

## HM77SM1

Author: Ivex
Size: 8.98 x 8.98 mm
PIN(s) | PAD
TYPE | SHAPE | SIZE | HOLE
1-2 | SMT | Rect | 1.52 x 8.38 mm | ---

Scale 2:1

## HM77SM2

Author: Ivex
Size: 11.26 x 11.4 mm
PIN(s) | PAD
TYPE | SHAPE | SIZE | HOLE
1-2 | SMT | Rect | 1.52 x 10.8 mm | ---

## HM77SM3

Author: Ivex
Size: 14.82 x 14.57 mm
PIN(s) | PAD
TYPE | SHAPE | SIZE | HOLE
1-2 | SMT | Rect | 2.54 x 13.97 mm | ---

Scale 1:1

## HM77SM4

Author: Ivex
Size: 16.09 x 15.33 mm
PIN(s) | PAD
TYPE | SHAPE | SIZE | HOLE
1-2 | SMT | Rect | 2.54 x 14.73 mm | ---

Scale 1:1

## HM77SM5

Author: Ivex
Size: 18.64 x 15.33 mm
PIN(s) | PAD
TYPE | SHAPE | SIZE | HOLE
1-2 | SMT | Rect | 2.54 x 14.73 mm | ---

Scale 1:1

## HM77SM6

Author: Ivex
Size: 20.67 x 18.13 mm
PIN(s) | PAD
TYPE | SHAPE | SIZE | HOLE
1-2 | SMT | Rect | 2.54 x 17.53 mm | ---

Scale 1:1

## LCI-20

Author: Ivex
Size: 8.98 x 8.22 mm
PIN(s) | PAD
TYPE | SHAPE | SIZE | HOLE
1-2 | SMT | Rect | 1.52 x 7.62 mm | ---

Scale 2:1

## LCI-30

## LCI-37

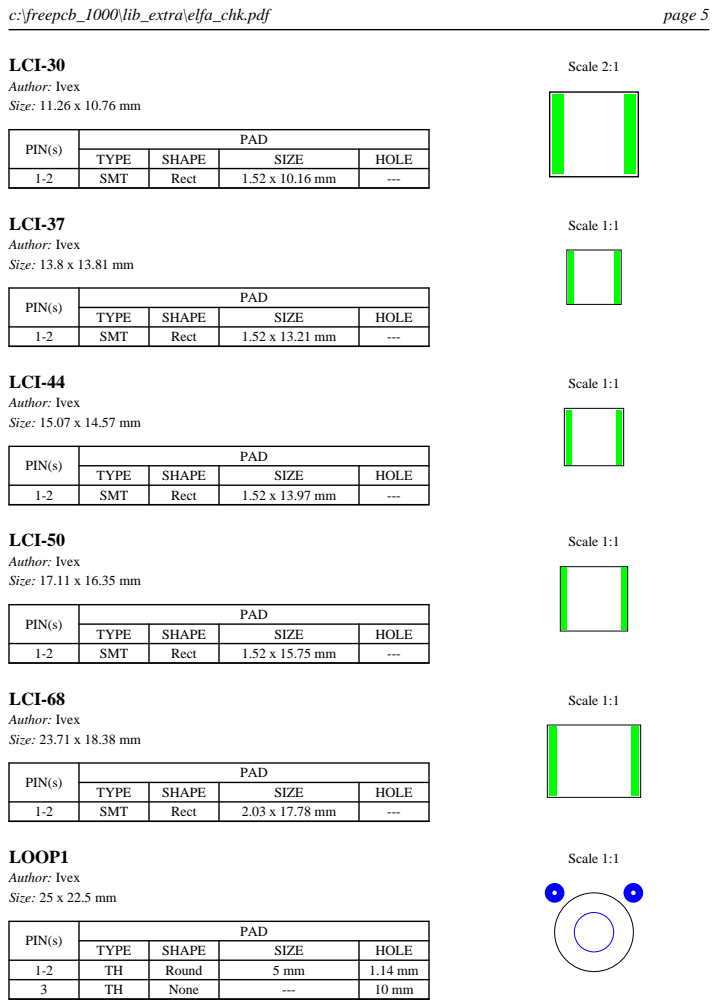
[picture p74: page 5]
Author: Ivex Size: 11.26 x 10.76 mm; Author: Ivex Size: 13.8 x 13.81 mm; Scale 1:1; LCI-44; Author: Ivex Size: 15.07 x 14.57 mm; LCI-50; Author: Ivex Size: 17.11 x 16.35 mm; LCI-68; Author: Ivex Size: 23.71 x 18.38 mm; LOOP1; Author: Ivex Size: 25 x 22.5 mm

PIN(s) | PAD

TYPE | SHAPE | SIZE | HOLE

1-2 | SMT | Rect | 1.52 x 10.16 mm | ---

1-2 | SMT | Rect | 1.52 x 13.21 mm | ---

1-2 | SMT | Rect | 1.52 x 13.97 mm | ---

1-2 | SMT | Rect | 1.52 x 15.75 mm | ---

1-2 | SMT | Rect | 2.03 x 17.78 mm | ---

1-2 | TH | Round | 5 mm | 1.14 mm
3 | TH | None | --- | 10 mm

## LOOP2

## LOOP3

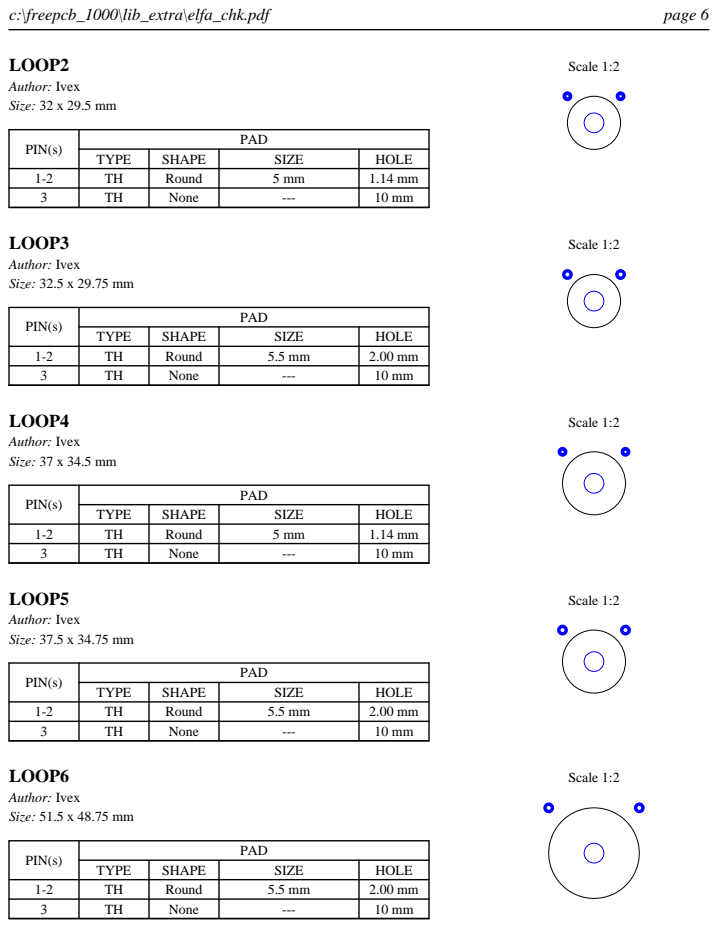
[picture p75: page 6]
Author: Ivex Size: 32 x 29.5 mm; Scale 1:2; Author: Ivex Size: 32.5 x 29.75 mm; LOOP4; Author: Ivex Size: 37 x 34.5 mm; LOOP5; Author: Ivex Size: 37.5 x 34.75 mm; LOOP6; Author: Ivex Size: 51.5 x 48.75 mm

PIN(s) | PAD

TYPE | SHAPE | SIZE | HOLE

1-2 | TH | Round | 5 mm | 1.14 mm
3 | TH | None | --- | 10 mm

1-2 | TH | Round | 5.5 mm | 2.00 mm

## LOOP7

## LOOP8

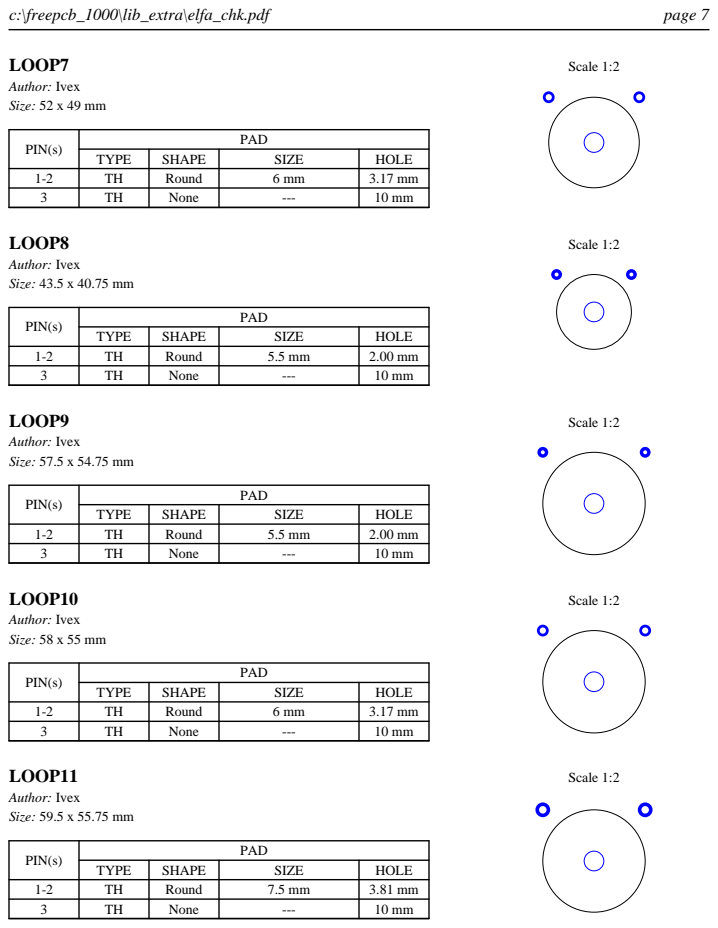
[picture p76: page 7]
Author: Ivex Size: 52 x 49 mm; Author: Ivex Size: 43.5 x 40.75 mm; Scale 1:2; LOOP9; Author: Ivex Size: 57.5 x 54.75 mm; LOOP10; Author: Ivex Size: 58 x 55 mm; LOOP11; Author: Ivex Size: 59.5 x 55.75 mm

PIN(s) | PAD

TYPE | SHAPE | SIZE | HOLE

1-2 | TH | Round | 6 mm | 3.17 mm
3 | TH | None | --- | 10 mm

1-2 | TH | Round | 5.5 mm | 2.00 mm

1-2 | TH | Round | 7.5 mm | 3.81 mm

## LOOP12

## LOOP13

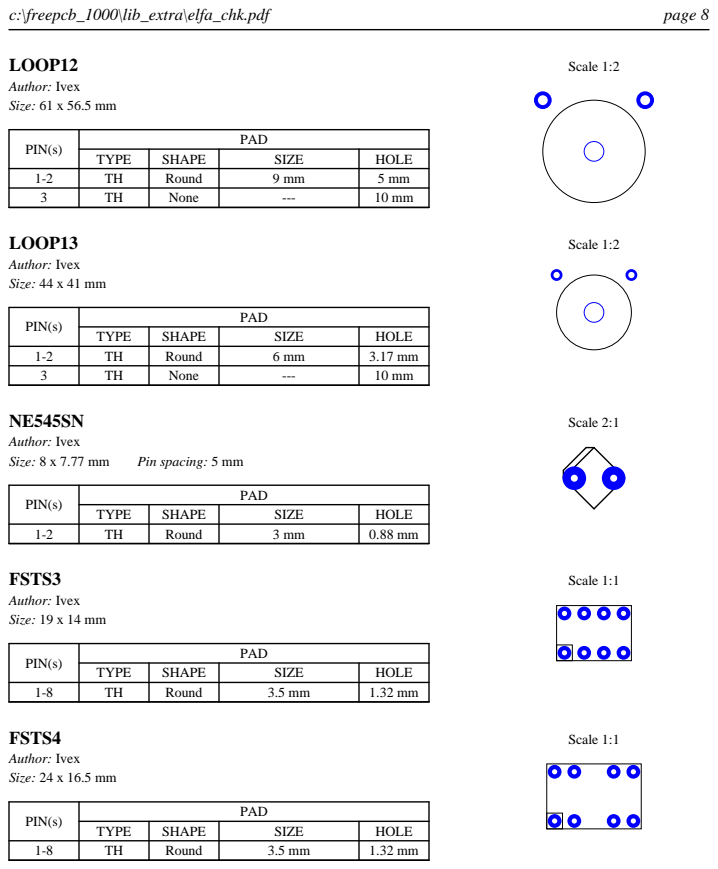
[picture p77: page 8]
Author: Ivex Size: 61 x 56.5 mm; Author: Ivex Size: 44 x 41 mm; Scale 1:2; Author: Ivex; Size: 8 x 7.77 mm; Pin spacing: 5 mm; Scale 2:1; FSTS3; Author: Ivex Size: 19 x 14 mm; Scale 1:1; FSTS4; Author: Ivex Size: 24 x 16.5 mm

PIN(s) | PAD

TYPE | SHAPE | SIZE | HOLE

1-2 | TH | Round | 9 mm | 5 mm
3 | TH | None | --- | 10 mm

1-2 | TH | Round | 6 mm | 3.17 mm

1-2 | TH | Round | 3 mm | 0.88 mm

1-8 | TH | Round | 3.5 mm | 1.32 mm

KM-2

KM-3

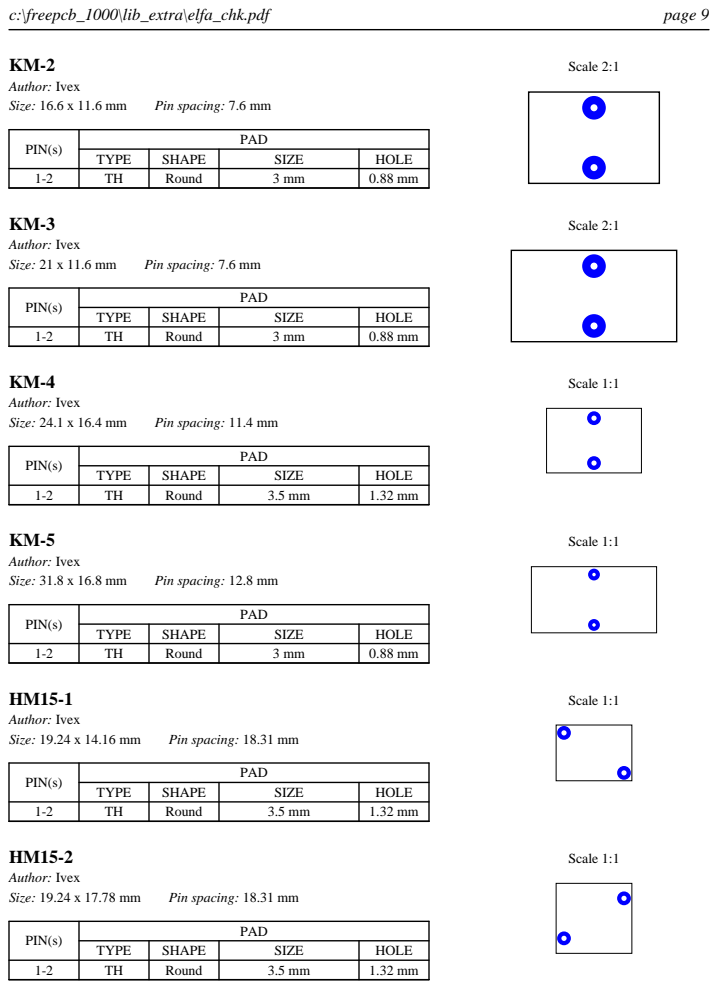
[picture p78: page 9]
Author: Ivex; Size: 16.6 x 11.6 mm; Pin spacing: 7.6 mm; Size: 21 x 11.6 mm; Scale 2:1; Size: 24.1 x 16.4 mm; Pin spacing: 11.4 mm; Scale 1:1; Size: 31.8 x 16.8 mm; Pin spacing: 12.8 mm; Size: 19.24 x 14.16 mm; Pin spacing: 18.31 mm; Size: 19.24 x 17.78 mm

PIN(s) | PAD

TYPE | SHAPE | SIZE | HOLE

1-2 | TH | Round | 3 mm | 0.88 mm

1-2 | TH | Round | 3.5 mm | 1.32 mm

RN112

RN222

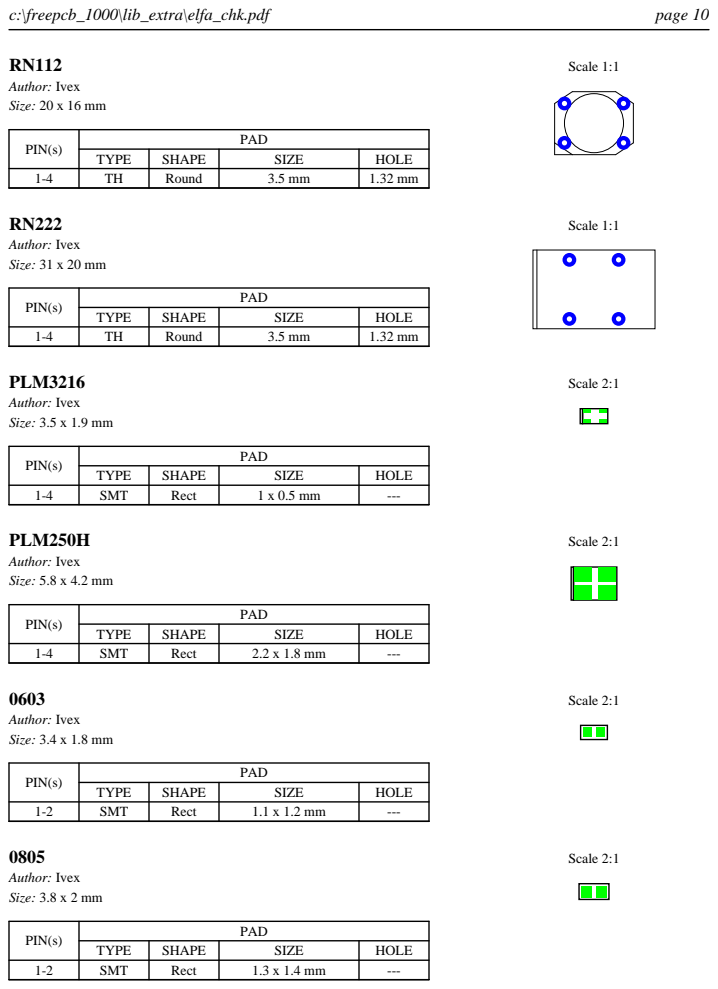
[picture p79: page 10]
Author: Ivex Size: 20 x 16 mm; Author: Ivex Size: 31 x 20 mm; Scale 1:1; PLM3216; Author: Ivex Size: 3.5 x 1.9 mm; Scale 2:1; PLM250H; Author: Ivex Size: 5.8 x 4.2 mm; Author: Ivex Size: 3.4 x 1.8 mm; Author: Ivex Size: 3.8 x 2 mm

PIN(s) | PAD

TYPE | SHAPE | SIZE | HOLE

1-4 | TH | Round | 3.5 mm | 1.32 mm

1-4 | SMT | Rect | 1 x 0.5 mm | ---

1-4 | SMT | Rect | 2.2 x 1.8 mm | ---

1-2 | SMT | Rect | 1.1 x 1.2 mm | ---

1-2 | SMT | Rect | 1.3 x 1.4 mm | ---
