PingvinOpenTag/LTAscetic/release_2(LCD,Joystck,TouchMemory,Reload,Antichiter,IrPowerControl,BattaryControl)/hardware/pcb/PCB_negative.pdf

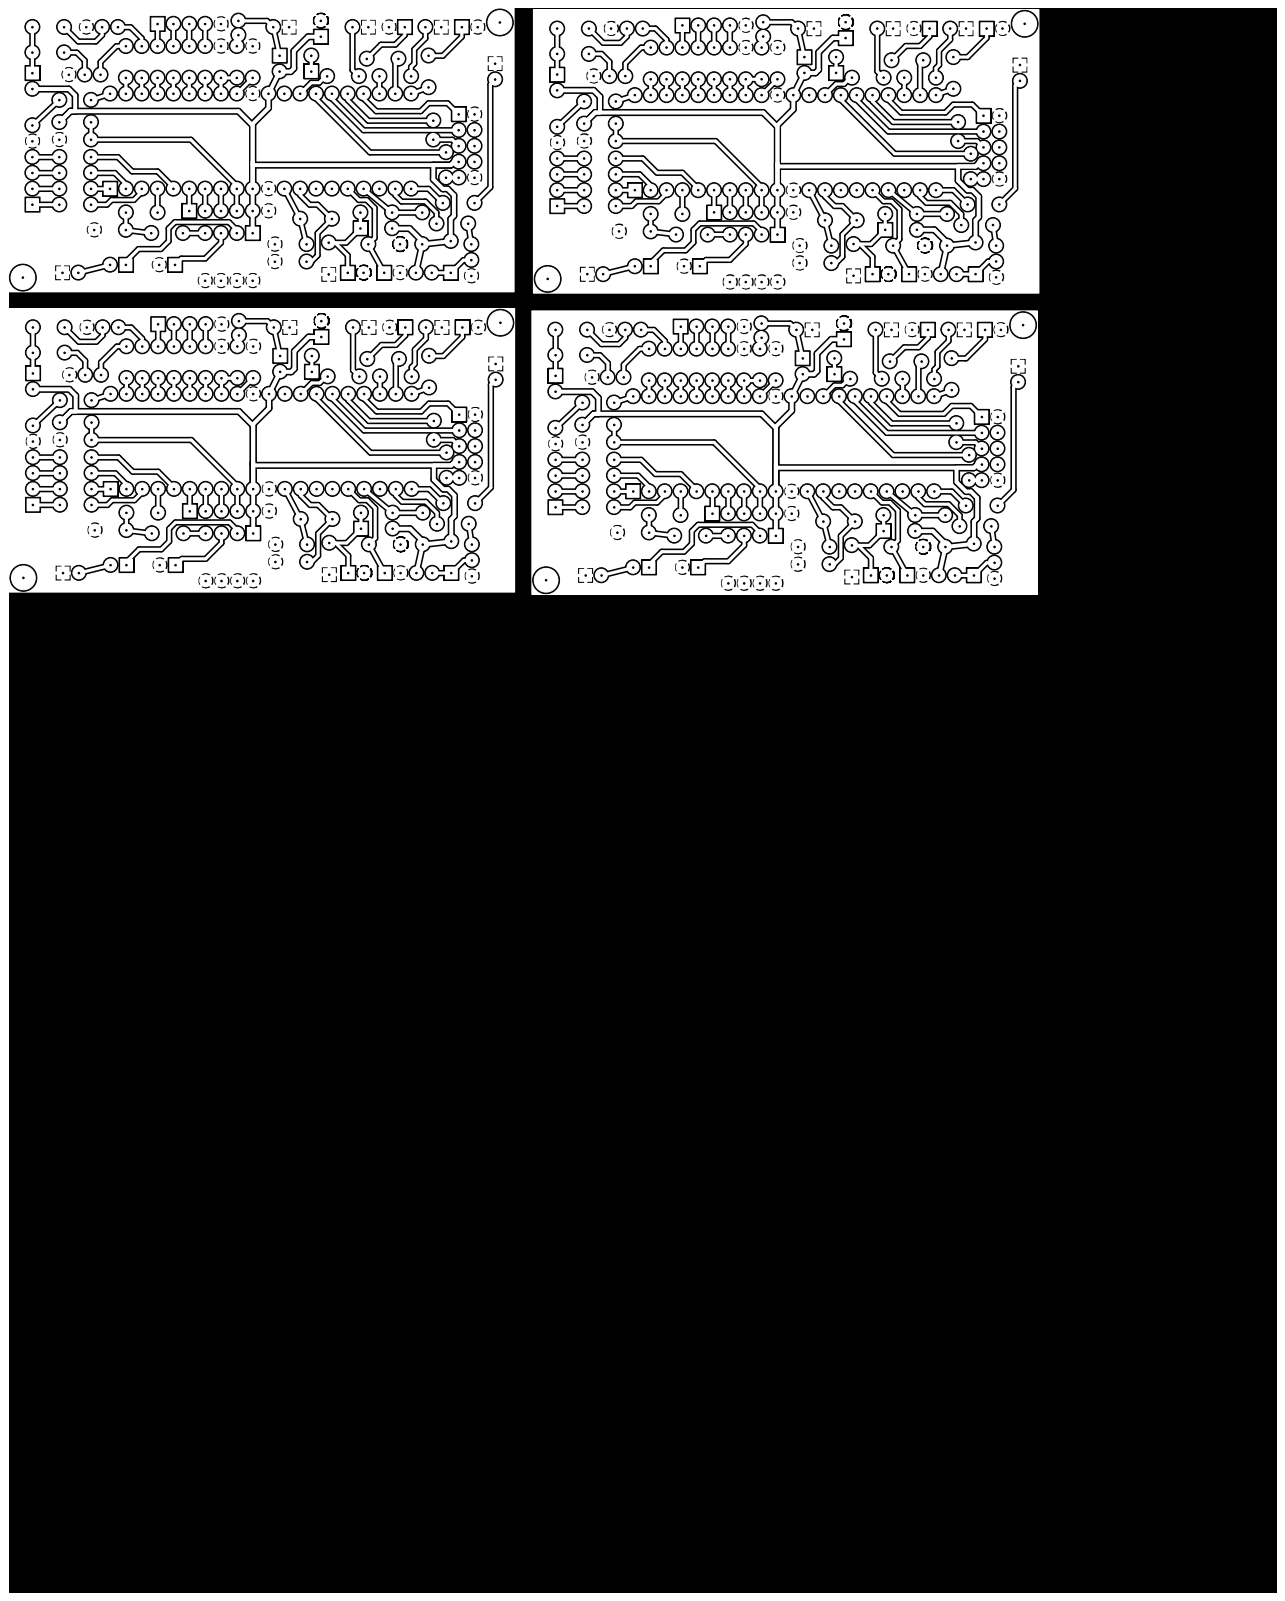
[picture p89: page 1]
