PingvinOpenTag/LTAscetic/release_3(all_thet_is_in_the_release_2,extern_EEPROM_RS232_BOOTLOADER)/hardware/pcb/PCB_lcd_shield_smd_negative.pdf

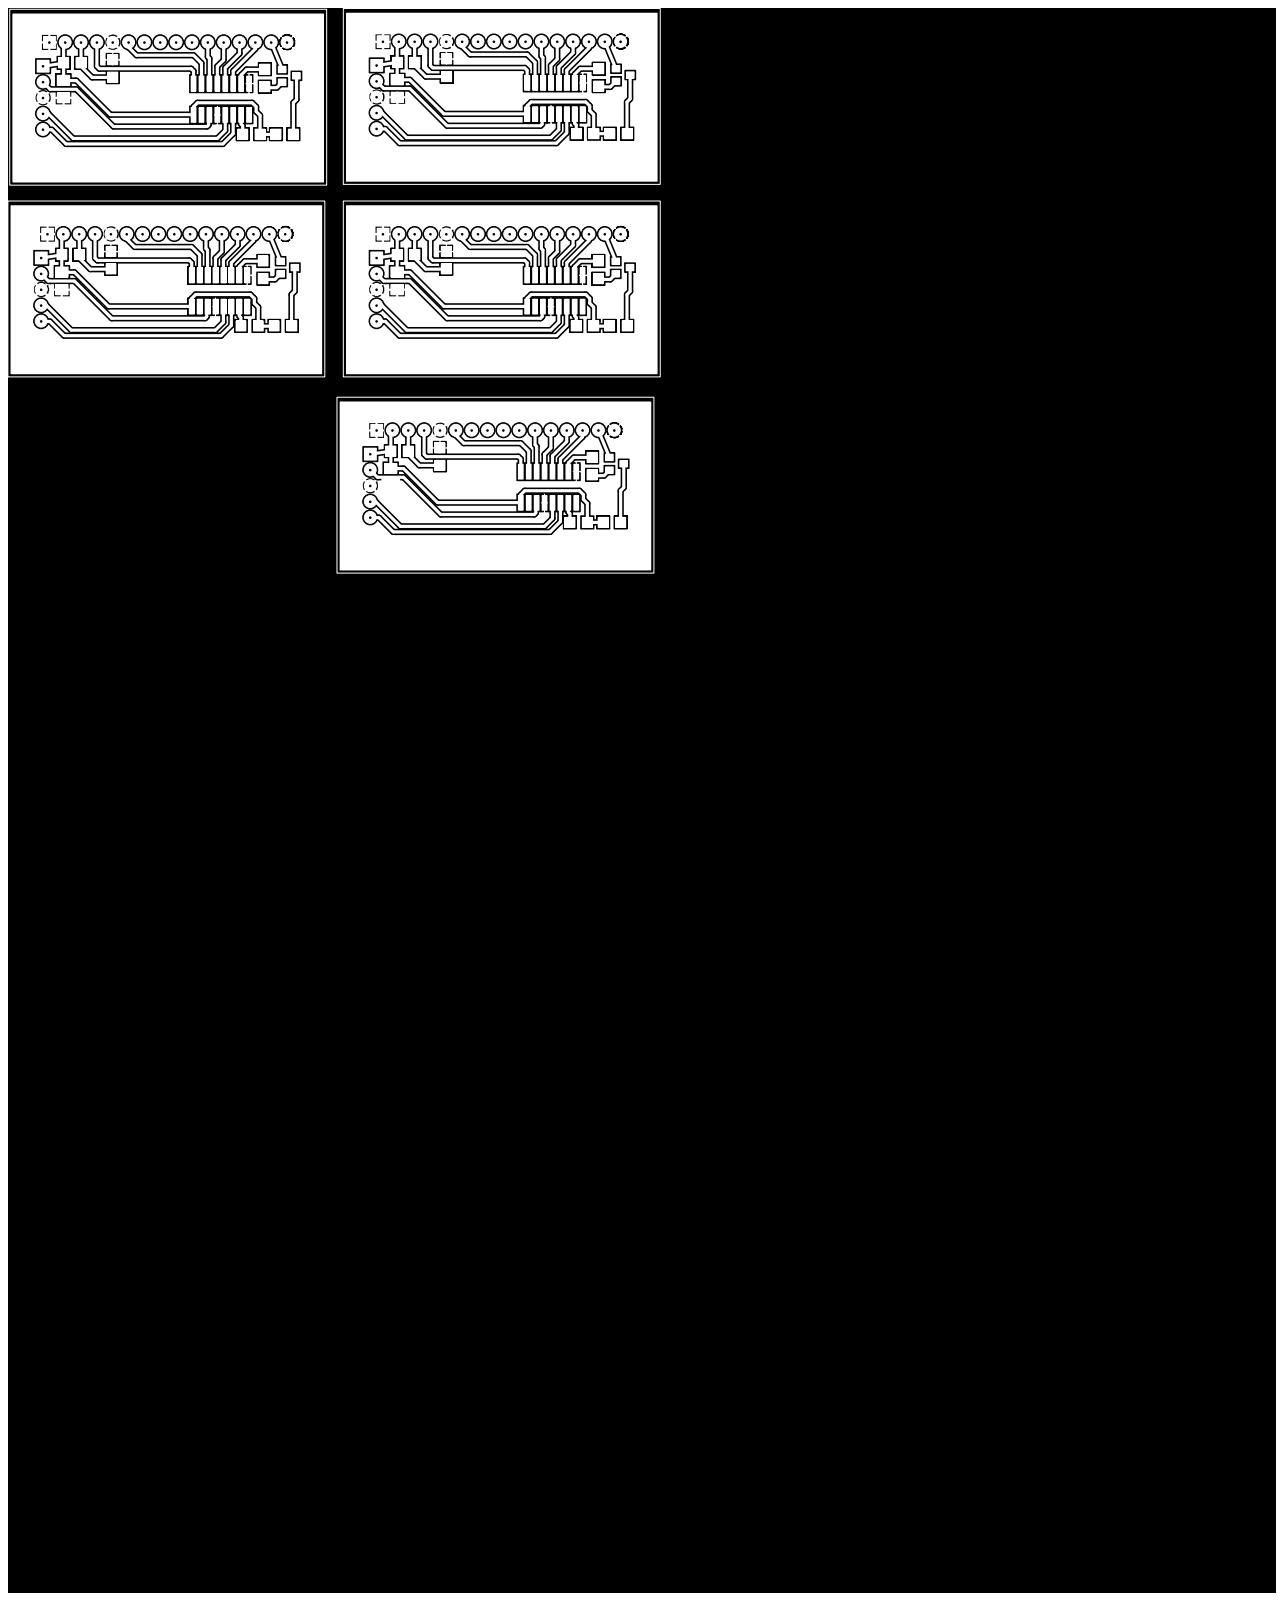
[picture p91: page 1]
