PingvinOpenTag/LTAscetic/release_1/hardware/pcb/PCB_negative.pdf

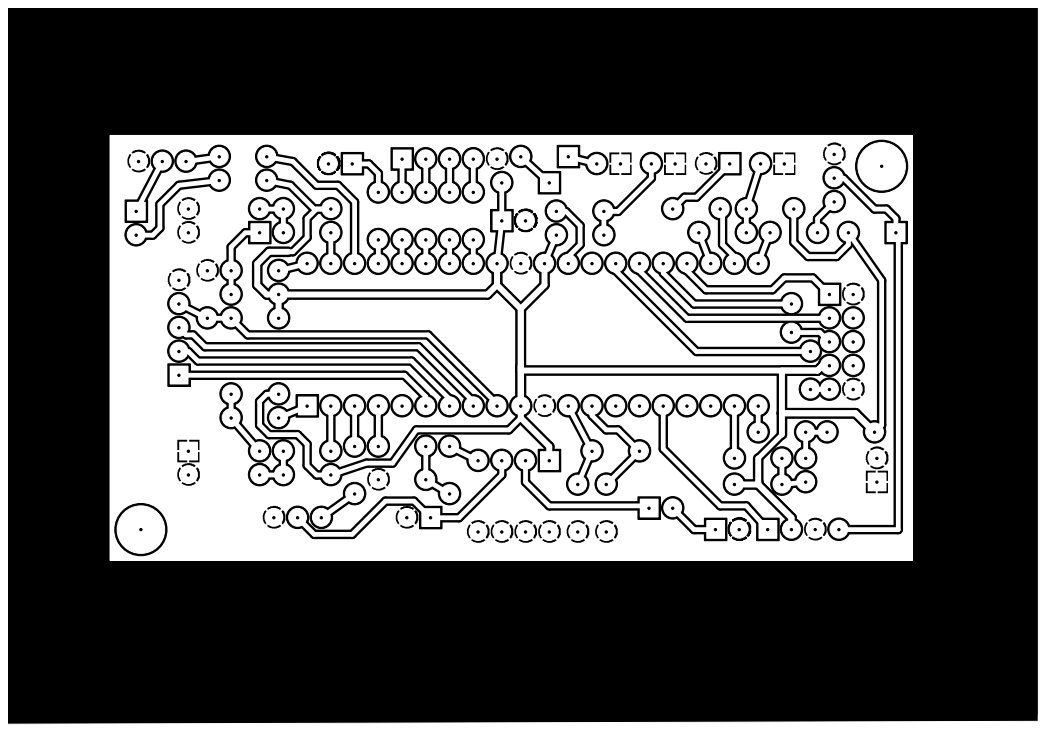
[picture p93: page 1]
