PingvinOpenTag/LTAscetic/release_1/hardware/pcb/PCB_positive.pdf

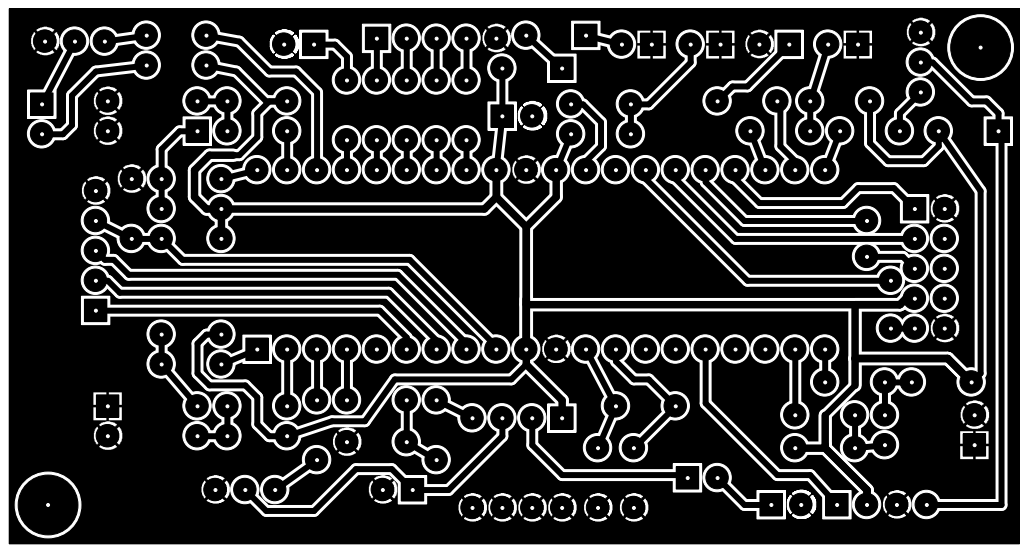
[picture p94: page 1]
