PingvinOpenTag/LTAscetic/internationalized_firmware/Ascet_3_1_LCD8x2_bluetooth_EN_RU/source/shift_regist_driver.h

#define SHIFT_REGISTER_DS_PORT PORTB //порт, к которуму подключен вход DS (данные) сдвигового регистра
#define SHIFT_REGISTER_SH_CP_PORT PORTB //порт, к которуму подключен вход SH_CP (тактовые импульсы) сдвигового регистра
#define SHIFT_REGISTER_ST_CP_PORT PORTB //порт, к которуму подключен вход ST_CP ("защлка" данных) сдвигового регистра

#define SHIFT_REGISTER_DS_DDR DDRB //управляющий регистр, к которуму подключен вход DS (данные) сдвигового регистра
#define SHIFT_REGISTER_SH_CP_DDR DDRB //управляющий регистр, к которуму подключен вход SH_CP (тактовые импульсы) сдвигового регистра
#define SHIFT_REGISTER_ST_CP_DDR DDRB //управляющий регистр, к которуму подключен вход ST_CP ("защлка" данных) сдвигового регистра

#define SHIFT_REGISTER_DS_PIN (1<<5) //вывод, к которуму подключен вход DS (данные) сдвигового регистра
#define SHIFT_REGISTER_SH_CP_PIN (1<<7) //вывод, к которуму подключен вход SH_CP (тактовые импульсы) сдвигового регистра
#define SHIFT_REGISTER_ST_CP_PIN (1<<6) //вывод, к которуму подключен вход ST_CP ("защлка" данных) сдвигового регистра




//все что ниже, при переопределении портов и пинов не трогаем!

#define SIHFT_REGISTER_DS_ON SHIFT_REGISTER_DS_PORT|=SHIFT_REGISTER_DS_PIN //выставляем в "1" сигнал DS  
#define SIHFT_REGISTER_DS_OFF SHIFT_REGISTER_DS_PORT&=~SHIFT_REGISTER_DS_PIN //выставляем в "0" сигнал DS  

#define SHIFT_REGISTER_SH_CP_ON SHIFT_REGISTER_SH_CP_PORT|=SHIFT_REGISTER_SH_CP_PIN //выставляем в "1" сигнал SH_CP
#define SHIFT_REGISTER_SH_CP_OFF SHIFT_REGISTER_SH_CP_PORT&=~SHIFT_REGISTER_SH_CP_PIN //выставляем в "0" сигнал SH_CP

#define SHIFT_REGISTER_ST_CP_ON SHIFT_REGISTER_ST_CP_PORT|=SHIFT_REGISTER_ST_CP_PIN ////выставляем в "1" сигнал ST_CP
#define SHIFT_REGISTER_ST_CP_OFF SHIFT_REGISTER_ST_CP_PORT&=~SHIFT_REGISTER_ST_CP_PIN ////выставляем в "0" сигнал ST_CP 


//настраиваем все управляющие сдвиговым регистром выводы как "выходы"
void init_shift_register(void){ //
SHIFT_REGISTER_DS_DDR|=SHIFT_REGISTER_DS_PIN;
SHIFT_REGISTER_SH_CP_DDR|= SHIFT_REGISTER_SH_CP_PIN;
SHIFT_REGISTER_ST_CP_DDR|= SHIFT_REGISTER_ST_CP_PIN;

SIHFT_REGISTER_DS_OFF;
SHIFT_REGISTER_SH_CP_OFF;
SHIFT_REGISTER_ST_CP_OFF;
};

void shift_register_set_data(volatile uint8_t shift_data){
volatile uint8_t mask;
mask = 0b10000000;
for (int i=0; i<8; i++)	
	{
		if ((mask&shift_data) ==0) 
		{SIHFT_REGISTER_DS_OFF;}	
//		if ((mask&shift_data)!=0) 
//		{SIHFT_REGISTER_DS_ON;}	
		
		else 
		{SIHFT_REGISTER_DS_ON;}
		SHIFT_REGISTER_SH_CP_ON;
//--//		asm("nop");
		SHIFT_REGISTER_SH_CP_OFF;
		mask = (mask>>1);
	}
	
	SHIFT_REGISTER_ST_CP_OFF;
//--//	asm("nop");
	SHIFT_REGISTER_ST_CP_ON;
}




/*
#define SPI_DDR  DDRB
#define SPI_PORT PORTB
#define SPI_SS   PB4//PB6//PB4
#define SPI_MOSI PB5 //+
#define SPI_MISO PB6
#define SPI_SCK  PB7 //+

void init_shift_register( void )
{
	//настраиваем выводы MOSI, SCL, SS на выход
	SPI_DDR = ( 1 << SPI_MOSI) | ( 1 << SPI_SCK) | ( 1 << SPI_SS ) | ( 1 << SPI_MISO );
	//выставляем SS в 1
	SPI_PORT |= ( 1 << SPI_SS );
	// разрешаем SPI, Master, режим 0, частота 1/4 от F_CPU, LSB first
	SPCR = ( 1 << SPE ) | ( 1 << MSTR ) | (1 << DORD ) | (1 << SPR1) | (1 << SPR0);
	//	SPSR = ( 1 << SPI2X ); //удвоение частоты SPI
}

void shift_register_set_data(volatile uint8_t shift_data)//(unsigned char b )
{
	unsigned char ret;
	//	while( !( SPSR & ( 1 << SPIF ) ) ); //ждем окончания передачи
	SPDR = shift_data;//b;                           //передаваемые данные
	while( !( SPSR & ( 1 << SPIF ) ) ); //ждем окончания передачи
	ret = SPDR;                         //считываем принятые данные
	//	SPI_PORT &= ~(1 << SPI_SS );        //сбрасываем SS в 0
	//	SPI_PORT |= ( 1 << SPI_SS );        //выставляем SS в 1
	
	SPI_PORT |= ( 1 << SPI_MISO );        //выставляем SS в 1
	SPI_PORT &= ~(1 << SPI_MISO);        //сбрасываем SS в 0



	//	return ret;
}

*/

void shift_register_clean(void){
shift_register_set_data(0);
}
